IanSB/RGBtoHDMI/vhdl_RGB_12bit/RGBtoHDMI.vhdl

----------------------------------------------------------------------------------
-- Engineer:            David Banks & Ian Bradbury
--
-- Create Date:         15/7/2018
-- Module Name:         vhdl_RGB_12bit CPLD
-- Project Name:        vhdl_RGB_12bit
-- Target Devices:      XC9572XL
--
-- Version:             1.0
--
----------------------------------------------------------------------------------
library ieee;
use ieee.std_logic_1164.all;
use ieee.numeric_std.all;

entity vhdl_RGB_12bit is
    Port (
        -- From RGB Connector
        R3_I:      in    std_logic;
        G3_I:      in    std_logic;
        B3_I:      in    std_logic;
        R2_I:      in    std_logic;
        G2_I:      in    std_logic;
        B2_I:      in    std_logic;
        R1_I:      in    std_logic;
        G1_I:      in    std_logic;
        B1_I:      in    std_logic;
        R0_I:      in    std_logic;
        G0_I:      in    std_logic;
        B0_I:      in    std_logic;

        csync_I:   in    std_logic;
        vsync_I:   in    std_logic;

        analog:    inout std_logic;

        -- From Pi
        clk:       in    std_logic;
        sp_clken:  in    std_logic;

        -- To PI GPIO
        quad:      inout std_logic_vector(11 downto 0);
        psync:     out   std_logic;
        csync:     out   std_logic;

        -- User interface
        version:   in    std_logic
    );
end vhdl_RGB_12bit;

architecture Behavorial of vhdl_RGB_12bit is

    -- Version number: Design_Major_Minor
    -- Design: 0 = BBC CPLD
    --         1 = Alternative CPLD
    --         2 = Atom CPLD
    --         3 = six bit CPLD (if required);
    --         4 = RGB CPLD (TTL)
    --         C = RGB CPLD (Analog)

    constant VERSION_NUM_RGB_TTL    : std_logic_vector(11 downto 0) := x"495";
    constant VERSION_NUM_RGB_ANALOG : std_logic_vector(11 downto 0) := x"C95";

    -- The sampling counter serves several purposes:
    -- 1. Counts the delay the rising edge of nCSYNC and the first pixel
    -- 2. Counts within each pixel (bits 0, 1, 2, 3)
    -- 3. Counts multiple pixels if less than 9/12 bpp
    -- 4. Handles double buffering of alternative quad pixels (bit 5)
    --
    -- At the moment we don't count pixels with the line, the Pi does that

    signal counter  : unsigned(8 downto 0);

    -- synchronisation signals
    signal csync_counter : unsigned(1 downto 0);
    signal csync1        : std_logic;
    signal csync2        : std_logic;
    signal last          : std_logic;
    signal mux_sync      : std_logic;
    signal clamp_pulse   : std_logic;
    signal clamp_enable  : std_logic;
    signal latched_vsync : std_logic;
    signal edge_detected : std_logic;

    -- RGB Input Mux
    signal R3       :std_logic;
    signal G3       :std_logic;
    signal B3       :std_logic;
    signal R2       :std_logic;
    signal G2       :std_logic;
    signal B2       :std_logic;

     -- Sampling points
    constant INIT_SAMPLING_POINTS : std_logic_vector(15 downto 0) := "0000000000000000";
    signal sp_reg   : std_logic_vector(15 downto 0) := INIT_SAMPLING_POINTS;

    -- Break out of sp_reg
    signal offset     : std_logic_vector(3 downto 0);
    signal delay      : unsigned(1 downto 0);
    signal edge       : std_logic;
    signal rate       : std_logic_vector(1 downto 0);
    signal rateswitch : std_logic;
    signal invert     : std_logic;
    signal divider    : unsigned(1 downto 0);
    signal divdel2    : std_logic;
    signal mux        : std_logic;
	 signal clamp_on   : std_logic;    
	 
	 -- optional top bits of divider and delay	 
    signal divider2   : std_logic;
    signal delay2     : unsigned(1 downto 0);

	 
	 
    -- Shift registers for pixel samples

    signal shift_R  : std_logic_vector(3 downto 0);
    signal shift_G  : std_logic_vector(3 downto 0);
    signal shift_B  : std_logic_vector(3 downto 0);

    -- Sample pixel on next clock; pipelined to reduce the number of product terms

    signal sampleR   : std_logic;
    signal sampleG   : std_logic;
    signal sampleB   : std_logic;

    -- New sample available, toggle psync on next cycle

    signal toggle          : std_logic;

    -- rate = 00 is 3 bit capture with clamp_on 0/1 = clamp off/on (rateswitch used to add delay to leading edge)
    -- rate = 01 and rateswitch = '0' is 6 bit capture with clamp_on 0/1 = clamp off/on
    -- rate = 01 and rateswitch = '1' is 6 bit capture with 3 bit to 4 level encoding (clamp not usable in 4 level mode)
    -- rate = 10 and rateswitch = '0' is 1 bit capture on G3 with clamp_on 0/1 = clamp off/on, divdel2 used as extra delay bit
    -- rate = 10 and rateswitch = '1' is 1 bit capture on vsync with clamp_on 0/1 = clamp off/on, divdel2 used as extra delay bit
    -- rate = 11 and rateswitch = '0' and clamp_on = 0 is 9 bit capture using vsync_I as replacement G1 bit (will work on 8 bit board)
    -- rate = 11 and rateswitch = '0' and clamp_on = 1 is 12 bit capture
    -- rate = 11 and rateswitch = '1' is 9 bit capture with blanking on B3_I

begin
    offset     <= sp_reg(3 downto 0);
    delay      <= unsigned(sp_reg(5 downto 4));
    edge       <= sp_reg(6);
    rate       <= sp_reg(8 downto 7);
    rateswitch <= sp_reg(9);
    invert     <= sp_reg(10);
    divider    <= unsigned(sp_reg(12 downto 11));
    divdel2    <= sp_reg(13);
    mux        <= sp_reg(14);
clamp_on        <= sp_reg(15);
    mux_sync <= vsync_I when mux = '1' and version = '1' else csync_I;

    delay2 <= '0' & divdel2 when rate = "10" else "10";   --require 3 bits of delay plus leading zero in 1bpp mode

    G3 <= G2_I when vsync_I = '1' else G3_I;
    G2 <= G3_I when vsync_I = '1' else G2_I;

    B3 <= B2_I when B1_I = '1' else B3_I;
    B2 <= B3_I when B1_I = '1' else B2_I;

    R3 <= R2_I when R1_I = '1' else R3_I;
    R2 <= R3_I when R1_I = '1' else R2_I;

    process(clk)
    begin
        if rising_edge(clk) then
            -- synchronize CSYNC to the sampling clock
            csync1 <= mux_sync xor invert;

            -- De-glitch CSYNC
            --    csync1 is the possibly glitchy input
            --    csync2 is the filtered output
            if csync1 = csync2 then
                -- output same as input, reset the counter
                csync_counter <= to_unsigned(0, csync_counter'length);
            else
                -- output different to input
                csync_counter <= csync_counter + 1;
                -- if the difference lasts for N-1 cycles, update the output
                --if rate = "00" and edge = '1' and rateswitch = '1' then
                --    if csync_counter = 255 then
                --        csync2 <= csync1;
                --    end if;
                --else
                    if csync_counter(1 downto 0) = 3 then
                        csync2 <= csync1;
                    end if;
                --end if;
            end if;

            last <= csync2;

            if rate = "10" then
                divider2 <= '0';
            else
                divider2 <= divdel2;
            end if;

            -- pipeline leading and trailing edge detection
            if (edge = '0' and last = '0' and csync2 = '1') or (edge = '1' and last = '1' and csync2 = '0') then
                edge_detected <= '1';
            else
                edge_detected <= '0';
            end if;

            -- Counter is used to find sampling point for first pixel
            -- reset counter on the rising edge of csync
            if edge_detected = '1' then
                counter(8 downto 0) <= '1' & delay2 & delay & "0000";
                latched_vsync <= '0';           
            else
                if counter(3 downto 0) = unsigned(offset) then
                    if rate = "10" then
                        sampleR <= not(counter(4));
                        sampleB <= counter(4);
                    else
                        sampleR <= '1';
                        sampleB <= '1';
                    end if;
                    sampleG <= '1';
                else
                    sampleR <= '0';
                    sampleB <= '0';
                    sampleG <= '0';
                end if;
                if (divider2 & divider) = "000" then
                    if counter(3 downto 0) /= 2 then
                        if counter(counter'left) = '1' then
                            counter <= counter + 1;
                        else
                            counter(counter'left - 1 downto 0) <= counter(counter'left - 1 downto 0) + 1;
                        end if;
                    else
                        if counter(counter'left) = '1' then
                            counter <= counter + 14;
                        else
                            counter(counter'left - 1 downto 0) <= counter(counter'left - 1 downto 0) + 14;
                        end if;
                    end if;
                elsif counter(3 downto 0) /= (divider2 & divider & '1') then
                    if counter(counter'left) = '1' then
                        counter <= counter + 1;
                    else
                        counter(counter'left - 1 downto 0) <= counter(counter'left - 1 downto 0) + 1;
                    end if;
                elsif counter(counter'left) = '1' then
                    counter <= counter + (not(divider2 & divider) & '1');
                else
                    counter(counter'left - 1 downto 0) <= counter(counter'left - 1 downto 0) + (not(divider2 & divider) & '1');
                end if;
            end if;


            -- R Sample/shift register
            if sampleR = '1' then
                if rate = "11" and rateswitch = '0' and clamp_on = '1' then
                    shift_R <= R1_I & G2_I & B3_I & B0_I;             -- 12 bpp
                elsif rate = "11" and rateswitch = '0' and clamp_on = '0'  then
                    shift_R <= R1_I & G2_I & B3_I & B3_I;             -- 9 bpp
                elsif rate = "11" and rateswitch = '1' then
                    shift_R <= (R1_I and B3_I) & (G2_I and B3_I) & B3_I & (B0_I and B3_I);  -- 9 bpp lo blanked
                elsif rate = "10" and rateswitch = '0' then
                    shift_R <= G3_I & shift_R(3 downto 1);            -- 1 bpp on G3
                elsif rate = "10" and rateswitch = '1' then
                    shift_R <= vsync_I & shift_R(3 downto 1);         -- 1 bpp on Vsync
                elsif rate = "01" and rateswitch = '1' then
                    shift_R <= R2 & R3 & shift_R(3 downto 2);         -- 6 bpp 4 level
                elsif rate = "01" and rateswitch = '0' then
                    shift_R <= R2_I & R3_I & shift_R(3 downto 2);     -- 6 bpp
                else
                    shift_R <= R3_I & shift_R(3 downto 1);            -- 3 bpp
                end if;
            end if;

            -- G Sample/shift register
            if sampleG = '1' then
                if latched_vsync = '0' then
                    latched_vsync <= vsync_I;
                end if;
                if rate = "11" and rateswitch = '0' and clamp_on = '1' then
                    shift_G <= R2_I & G3_I & G0_I & B1_I;             -- 12 bpp
                elsif rate = "11" and rateswitch = '0' and clamp_on = '0' then
                    shift_G <= R2_I & G3_I & G3_I & B1_I;             -- 9 bpp
                elsif rate = "11" and rateswitch = '1' then
                    shift_G <= (R2_I and B3_I) & G3_I & (G0_I and B3_I) & (B1_I and B3_I);  -- 9 bpp lo blanked
                elsif rate = "01" and rateswitch = '1' then
                    shift_G <= G2 & G3 & shift_G(3 downto 2);         -- 6 bpp 4 level
                elsif rate = "01" and rateswitch = '0' then
                    shift_G <= G2_I & G3_I & shift_G(3 downto 2);     -- 6 bpp
                else
                    shift_G <= G3_I & shift_G(3 downto 1);            -- 3 bpp
                end if;
            end if;

            -- B Sample/shift register
             if sampleB = '1' then
                if rate = "11" and rateswitch = '0' and clamp_on = '1' then
                    shift_B <= R3_I & R0_I & G1_I & B2_I;             -- 12 bpp
                elsif rate = "11" and rateswitch = '0' and clamp_on = '0' then
                    shift_B <= R3_I & R3_I & vsync_I & B2_I;          -- 9 bpp with G1 on vsync_I
                elsif rate = "11" and rateswitch = '1' then
                    shift_B <= R3_I & (R0_I and B3_I) & (G1_I and B3_I) & (B2_I and B3_I);  -- 9 bpp lo blanked
                elsif rate = "10" and rateswitch = '0' then
                    shift_B <= G3_I & shift_B(3 downto 1);            -- 1 bpp on G3
                elsif rate = "10" and rateswitch = '1' then
                    shift_B <= vsync_I & shift_B(3 downto 1);         -- 1 bpp on Vsync
                elsif rate = "01" and rateswitch = '1' then
                    shift_B <= B2 & B3 & shift_B(3 downto 2);         -- 6 bpp 4 level
                elsif rate = "01" and rateswitch = '0' then
                    shift_B <= B2_I & B3_I & shift_B(3 downto 2);     -- 6 bpp
                else
                    shift_B <= B3_I & shift_B(3 downto 1);            -- 3 bpp
                end if;
            end if;

            -- Pipeline when to update the quad

            if ((rate = "00" and counter(5 downto 0) = 0) or      --  3 bpp
                (rate = "01" and counter(4 downto 0) = 0) or      --  6 bpp
                (rate = "10" and counter(6 downto 0) = 0) or      --  1 bpp
                (rate = "11" and counter(3 downto 0) = 0)) then   --  9 or 12 bpp
                toggle <= '1';  -- toggle is asserted in cycle 1
            else
                toggle <= '0';
            end if;
            if sp_clken = '0' then  
					-- Output quad register
					if version = '0' then
						 if analog = '1' then
							  quad <= VERSION_NUM_RGB_ANALOG;
						 else
							  quad <= VERSION_NUM_RGB_TTL;
						 end if;
					elsif toggle = '1' then
						 -- quad changes at the start of cycle 2
						 quad(11) <= shift_B(3);
						 quad(10) <= shift_G(3);
						 quad(9)  <= shift_R(3);
						 quad(8)  <= shift_B(2);
						 quad(7)  <= shift_G(2);
						 quad(6)  <= shift_R(2);
						 quad(5)  <= shift_B(1);
						 quad(4)  <= shift_G(1);
						 quad(3)  <= shift_R(1);
						 quad(2)  <= shift_B(0);
						 quad(1)  <= shift_G(0);
						 quad(0)  <= shift_R(0);
					end if;
				else
					if version = '1' then
					    if quad(8) = '0' then 
							  sp_reg(7 downto 0) <= quad(7 downto 0);	
                   else
						     sp_reg(15 downto 8) <= quad(7 downto 0);	
						 end if;					
					end if;
				end if;

            -- Output a skewed version of psync
            if version = '0' then
                psync <= vsync_I;
            elsif counter(counter'left) = '1' then
                psync <= '0';
            elsif counter(3 downto 0) = 2 then -- comparing with N gives N-1 cycles of skew
                if rate = "00" then
                    psync <= counter(6);       --  3 bpp: one edge for every 4 pixels
                elsif rate = "01" then
                    psync <= counter(5);       --  6 bpp: one edge for every 2 pixels
                elsif rate = "10" then
                    psync <= counter(7);       --  1 bpp: one edge for every 8 pixels
                elsif rate = "11" then
                    psync <= counter(4);       --  9/12 bpp: one edge for every pixel
                end if;
            end if;
        end if;
    end process;

    csync <= csync2 when version = '1' else latched_vsync; -- output the registered version to save a macro-cell

    -- csync2 is cleaned but delayed so OR with csync1 to remove delay on trailing edge of sync pulse
    -- clamp not usable in 4 LEVEL mode (rate = 10) or 8/12 bit mode (rate = 11) so use as multiplex signal instead
    clamp_pulse <= not(csync1 or csync2);
    clamp_enable <= '1' when mux = '1' else version;
    -- spdata is overloaded as clamp on/off
    analog <= 'Z' when clamp_enable = '0' else clamp_pulse and clamp_on;

end Behavorial;
