IanSB/RGBtoHDMI/src/osd.c

#include <stdio.h>
#include <stdlib.h>
#include <string.h>
#include <inttypes.h>
#include <ctype.h>
#include "defs.h"
#include "cpld.h"
#include "geometry.h"
#include "gitversion.h"
#include "info.h"
#include "logging.h"
#include "osd.h"
#include "rpi-gpio.h"
#include "rpi-mailbox.h"
#include "rpi-mailbox-interface.h"
#include "saa5050_font.h"
#include "8x8_font.h"
#include "rgb_to_fb.h"
#include "rgb_to_hdmi.h"
#include "filesystem.h"
#include "fatfs/ff.h"
#include "jtag/update_cpld.h"

// =============================================================
// Definitions for the size of the OSD
// =============================================================

#define NLINES         30

#define FONT_THRESHOLD    25

#define LINELEN        42

#define MAX_MENU_DEPTH  4

#define DEFAULT_CPLD_FIRMWARE_DIR "/cpld_firmware/recovery"

// =============================================================
// Definitions for the key press interface
// =============================================================

#define LONG_KEY_PRESS_DURATION 25

// =============================================================
// Main states that the OSD can be in
// =============================================================

typedef enum {
   IDLE,          // Wait for button to be pressed
   DURATION,      // Determine whether short or long button press

   MIN_ACTION,    // Marker state, never actually used

   // The next N states are the pre-defined action states
   // At most 6 of these can be bound to button presses (3 buttons, long/short)
   A0_LAUNCH,     // Action 0: Launch menu system
   A1_CAPTURE,    // Action 1: Screen capture
   A2_CLOCK_CAL,  // Action 2: HDMI clock calibration
   A3_AUTO_CAL,   // Action 3: Auto calibration
   A4_SCANLINES,  // Action 4: Toggle scanlines
   A5_SPARE,      // Action 5: Spare
   A6_SPARE,      // Action 6: Spare
   A7_SPARE,      // Action 7: Spare

   MAX_ACTION,    // Marker state, never actually used

   CLOCK_CAL0,    // Intermediate state in clock calibration
   CLOCK_CAL1,    // Intermediate state in clock calibration
   MENU,          // Browsing a menu
   PARAM,         // Changing the value of a menu item
   INFO           // Viewing an info panel
} osd_state_t;

// =============================================================
// Friently names for certain OSD feature values
// =============================================================


static char *default_palette_names[] = {
   "RGB",
   "RGBI",
   "RGBI_(CGA)",
   "RGBI_(Spectrum)",
   "RGBrgb_(Spectrum)",
   "RGBrgb_(Amstrad)",
   "RrGgBb_(EGA)",
   "MDA-Hercules",
   "Dragon-CoCo",
   "Dragon-CoCo_Full",
   "Dragon-CoCo_Emu",
   "Atom_MKII",
   "Atom_MKII_Plus",
   "Atom_MKII_Full",
   "Mono_(2_level)",
   "Mono_(3_level)",
   "Mono_(4_level)",
   "Mono_(6_level)",
 //  "TI-99-4a_14Col",
   "Spectrum_48K_9Col",
   "Colour_Genie_S24",
   "Colour_Genie_S25",
   "Colour_Genie_N25"
};

static const char *palette_control_names[] = {
   "Off",
   "In Band Commands",
   "NTSC Artifacting"
};

static const char *return_names[] = {
   "Start",
   "End"
};

static const char *vlockmode_names[] = {
   "Genlocked (Exact)",
   "1000ppm Fast",
   "2000ppm Fast",
   "Unlocked",
   "2000ppm Slow",
   "1000ppm Slow"
};

static const char *deinterlace_names[] = {
   "None",
   "Simple Bob",
   "Simple Motion 1",
   "Simple Motion 2",
   "Simple Motion 3",
   "Simple Motion 4",
   "Advanced Motion"
};

#ifdef MULTI_BUFFER
static const char *nbuffer_names[] = {
   "Single buffered",
   "Double buffered",
   "Triple buffered",
   "Quadruple buffered"
};
#endif

static const char *autoswitch_names[] = {
   "Off",
   "Sub-Profile",
   "BBC Mode 7"
};

static const char *overscan_names[] = {
   "Auto",
   "Maximum",
   "Halfway",
   "Minimum"
};

static const char *colour_names[] = {
   "Normal",
   "Monochrome",
   "Green",
   "Amber"
};

static const char *invert_names[] = {
   "Normal",
   "Invert RGB/YUV",
   "Invert G/Y"
};

static const char *scaling_names[] = {
   "Integer / Sharp",
   "Integer / Soft",
   "Integer / Very Soft",
   "Fill 4:3 / Soft",
   "Fill 4:3 / Very Soft",
   "Fill All / Soft",
   "Fill All / Very Soft"
};

static const char *frontend_names[] = {
   "3 BIT RGB",
   "Atom",
   "6 BIT RGB",
   "6 BIT RGB Analog Issue 3",
   "6 BIT RGB Analog Issue 2",   
   "6 BIT RGB Analog Issue 1A",
   "6 BIT RGB Analog Issue 1B",
   "6 BIT YUV Analog Issue 3",
   "6 BIT YUV Analog Issue 2"   
};

static const char *vlockspeed_names[] = {
   "Slow (333PPM)",
   "Medium (1000PPM)",
   "Fast (2000PPM)"
};

static const char *vlockadj_names[] = {
   "-5% to +5%",
   "Full Range",
   "Up to 260Mhz"
};

static const char *fontsize_names[] = {
   "Always 8x8",
   "Auto 12x20 4bpp",
   "Auto 12x20 8bpp"
};

static const char *even_scaling_names[] = {
   "Even",
   "Uneven (3:2>>4:3)"
};

// =============================================================
// Feature definitions
// =============================================================

enum {
   F_AUTOSWITCH,
   F_RESOLUTION,
   F_SCALING,
   F_FRONTEND,
   F_PROFILE,
   F_SUBPROFILE,
   F_PALETTE,
   F_PALETTECONTROL,
   F_DEINTERLACE,
   F_M7SCALING,
   F_NORMALSCALING,
   F_COLOUR,
   F_INVERT,
   F_SCANLINES,
   F_SCANLINESINT,
   F_OVERSCAN,
   F_CAPSCALE,
   F_FONTSIZE,
   F_BORDER,
   F_VSYNC,
   F_VLOCKMODE,
   F_VLOCKLINE,
   F_VLOCKSPEED,
   F_VLOCKADJ,
#ifdef MULTI_BUFFER
   F_NBUFFERS,
#endif
   F_RETURN,
   F_DEBUG
};

static param_t features[] = {
   {      F_AUTOSWITCH,       "Auto Switch",       "auto_switch", 0, NUM_AUTOSWITCHES - 1, 1 },
   {      F_RESOLUTION,        "Resolution",        "resolution", 0,                    0, 1 },
   {         F_SCALING,           "Scaling",           "scaling", 0,      NUM_SCALING - 1, 1 },
   {        F_FRONTEND,         "Interface",         "interface", 0,    NUM_FRONTENDS - 1, 1 },
   {         F_PROFILE,           "Profile",           "profile", 0,                    0, 1 },
   {      F_SUBPROFILE,       "Sub-Profile",        "subprofile", 0,                    0, 1 },
   {         F_PALETTE,           "Palette",           "palette", 0,                    0, 1 },
   {  F_PALETTECONTROL,   "Palette Control",   "palette_control", 0,     NUM_CONTROLS - 1, 1 },
   {     F_DEINTERLACE,"Teletext Deinterlace", "teletext_deinterlace", 0, NUM_DEINTERLACES - 1, 1 },
   {       F_M7SCALING,  "Teletext Scaling",     "teletext_scaling", 0,   NUM_ESCALINGS - 1, 1 },
   {   F_NORMALSCALING,"Progressive Scaling",    "progressive_scaling", 0, NUM_ESCALINGS - 1, 1 },
   {          F_COLOUR,     "Output Colour",     "output_colour", 0,      NUM_COLOURS - 1, 1 },
   {          F_INVERT,     "Output Invert",     "output_invert", 0,       NUM_INVERT - 1, 1 },
   {       F_SCANLINES,         "Scanlines",         "scanlines", 0,                    1, 1 },
   {    F_SCANLINESINT,    "Scanline Level",    "scanline_level", 0,                   15, 1 },
   {        F_OVERSCAN,          "Overscan",          "overscan", 0,     NUM_OVERSCAN - 1, 1 },
   {        F_CAPSCALE, "ScreenCap Scaling", "screencap_scaling", 0,                    1, 1 },
   {        F_FONTSIZE,         "Font Size",         "font_size", 0,     NUM_FONTSIZE - 1, 1 },
   {          F_BORDER,     "Border Colour",     "border_colour", 0,                  255, 1 },
   {           F_VSYNC,  "V Sync Indicator",   "vsync_indicator", 0,                    1, 1 },
   {       F_VLOCKMODE,       "V Lock Mode",        "vlock_mode", 0,         NUM_HDMI - 1, 1 },
   {       F_VLOCKLINE,      "Genlock Line",      "genlock_line",35,                  140, 1 },
   {      F_VLOCKSPEED,     "Genlock Speed",     "genlock_speed", 0,   NUM_VLOCKSPEED - 1, 1 },
   {        F_VLOCKADJ,    "Genlock Adjust",    "genlock_adjust", 0,     NUM_VLOCKADJ - 2, 1 },  //-2 so disables 260 mhz for now
#ifdef MULTI_BUFFER
   {        F_NBUFFERS,       "Num Buffers",       "num_buffers", 0,                    3, 1 },
#endif
   {          F_RETURN,   "Return Position",            "return", 0,                    1, 1 },
   {           F_DEBUG,             "Debug",             "debug", 0,                    1, 1 },
   {                -1,                NULL,                NULL, 0,                    0, 0 }
};

// =============================================================
// Menu definitions
// =============================================================


typedef enum {
   I_MENU,     // Item points to a sub-menu
   I_FEATURE,  // Item is a "feature" (i.e. managed by the osd)
   I_GEOMETRY, // Item is a "geometry" (i.e. managed by the geometry)
   I_PARAM,    // Item is a "parameter" (i.e. managed by the cpld)
   I_INFO,     // Item is an info screen
   I_BACK,     // Item is a link back to the previous menu
   I_SAVE,     // Item is a saving profile option
   I_RESTORE,  // Item is a restoring a profile option
   I_UPDATE,   // Item is a cpld update
   I_CALIBRATE // Item is a calibration update
} item_type_t;

typedef struct {
   item_type_t       type;
} base_menu_item_t;

typedef struct menu {
   char *name;
   void            (*rebuild)(struct menu *this);
   base_menu_item_t *items[];
} menu_t;

typedef struct {
   item_type_t       type;
   menu_t           *child;
} child_menu_item_t;

typedef struct {
   item_type_t       type;
   param_t          *param;
} param_menu_item_t;

typedef struct {
   item_type_t       type;
   char             *name;
   void            (*show_info)(int line);
} info_menu_item_t;

typedef struct {
   item_type_t       type;
   char             *name;
} back_menu_item_t;

typedef struct {
   item_type_t       type;
   char             *name;
} action_menu_item_t;

static void info_source_summary(int line);
static void info_system_summary(int line);
static void info_cal_summary(int line);
static void info_cal_detail(int line);
static void info_cal_raw(int line);
static void info_credits(int line);
static void info_reboot(int line);

static void rebuild_geometry_menu(menu_t *menu);
static void rebuild_sampling_menu(menu_t *menu);
static void rebuild_update_cpld_menu(menu_t *menu);

static info_menu_item_t source_summary_ref   = { I_INFO, "Source Summary",      info_source_summary};
static info_menu_item_t system_summary_ref   = { I_INFO, "System Summary",      info_system_summary};
static info_menu_item_t cal_summary_ref      = { I_INFO, "Calibration Summary", info_cal_summary};
static info_menu_item_t cal_detail_ref       = { I_INFO, "Calibration Detail",  info_cal_detail};
static info_menu_item_t cal_raw_ref          = { I_INFO, "Calibration Raw",     info_cal_raw};
static info_menu_item_t credits_ref          = { I_INFO, "Credits",             info_credits};
static info_menu_item_t reboot_ref           = { I_INFO, "Reboot",              info_reboot};

static back_menu_item_t back_ref             = { I_BACK, "Return"};
static action_menu_item_t save_ref           = { I_SAVE, "Save Configuration"};
static action_menu_item_t restore_ref        = { I_RESTORE, "Restore Default Configuration"};
static action_menu_item_t cal_sampling_ref   = { I_CALIBRATE, "Auto Calibrate Video Sampling"};


static menu_t update_cpld_menu = {
   "Update CPLD Menu",
   rebuild_update_cpld_menu,
   {
      // Allow space for max 30 params
      NULL,
      NULL,
      NULL,
      NULL,
      NULL,
      NULL,
      NULL,
      NULL,
      NULL,
      NULL,
      NULL,
      NULL,
      NULL,
      NULL,
      NULL,
      NULL,
      NULL,
      NULL,
      NULL,
      NULL,
      NULL,
      NULL,
      NULL,
      NULL,
      NULL,
      NULL,
      NULL,
      NULL,
      NULL,
      NULL,
      NULL
   }
};

static child_menu_item_t update_cpld_menu_ref = { I_MENU, &update_cpld_menu};

static menu_t info_menu = {
   "Info Menu",
   NULL,
   {
      (base_menu_item_t *) &back_ref,
      (base_menu_item_t *) &source_summary_ref,
      (base_menu_item_t *) &system_summary_ref,
      (base_menu_item_t *) &cal_summary_ref,
      (base_menu_item_t *) &cal_detail_ref,
      (base_menu_item_t *) &cal_raw_ref,
      (base_menu_item_t *) &credits_ref,
      (base_menu_item_t *) &reboot_ref,
      (base_menu_item_t *) &update_cpld_menu_ref,
      NULL
   }
};

static param_menu_item_t profile_ref         = { I_FEATURE, &features[F_PROFILE]        };
static param_menu_item_t subprofile_ref      = { I_FEATURE, &features[F_SUBPROFILE]     };
static param_menu_item_t resolution_ref      = { I_FEATURE, &features[F_RESOLUTION]     };
static param_menu_item_t scaling_ref         = { I_FEATURE, &features[F_SCALING]        };
static param_menu_item_t frontend_ref        = { I_FEATURE, &features[F_FRONTEND]       };
static param_menu_item_t overscan_ref        = { I_FEATURE, &features[F_OVERSCAN]       };
static param_menu_item_t capscale_ref        = { I_FEATURE, &features[F_CAPSCALE]       };
static param_menu_item_t border_ref          = { I_FEATURE, &features[F_BORDER]         };
static param_menu_item_t palettecontrol_ref  = { I_FEATURE, &features[F_PALETTECONTROL] };
static param_menu_item_t palette_ref         = { I_FEATURE, &features[F_PALETTE]        };
static param_menu_item_t deinterlace_ref     = { I_FEATURE, &features[F_DEINTERLACE]    };
static param_menu_item_t m7scaling_ref       = { I_FEATURE, &features[F_M7SCALING]      };
static param_menu_item_t normalscaling_ref   = { I_FEATURE, &features[F_NORMALSCALING]  };
static param_menu_item_t scanlines_ref       = { I_FEATURE, &features[F_SCANLINES]      };
static param_menu_item_t scanlinesint_ref    = { I_FEATURE, &features[F_SCANLINESINT]   };
static param_menu_item_t colour_ref          = { I_FEATURE, &features[F_COLOUR]         };
static param_menu_item_t invert_ref          = { I_FEATURE, &features[F_INVERT]         };
static param_menu_item_t fontsize_ref        = { I_FEATURE, &features[F_FONTSIZE]       };
static param_menu_item_t vsync_ref           = { I_FEATURE, &features[F_VSYNC]          };
static param_menu_item_t vlockmode_ref       = { I_FEATURE, &features[F_VLOCKMODE]      };
static param_menu_item_t vlockline_ref       = { I_FEATURE, &features[F_VLOCKLINE]      };
static param_menu_item_t vlockspeed_ref      = { I_FEATURE, &features[F_VLOCKSPEED]     };
static param_menu_item_t vlockadj_ref        = { I_FEATURE, &features[F_VLOCKADJ]       };
#ifdef MULTI_BUFFER
static param_menu_item_t nbuffers_ref        = { I_FEATURE, &features[F_NBUFFERS]       };
#endif
static param_menu_item_t autoswitch_ref      = { I_FEATURE, &features[F_AUTOSWITCH]     };
static param_menu_item_t return_ref          = { I_FEATURE, &features[F_RETURN]         };
static param_menu_item_t debug_ref           = { I_FEATURE, &features[F_DEBUG]          };

static menu_t preferences_menu = {
   "Preferences Menu",
   NULL,
   {
      (base_menu_item_t *) &back_ref,
      (base_menu_item_t *) &palette_ref,
      (base_menu_item_t *) &colour_ref,
      (base_menu_item_t *) &invert_ref,
      (base_menu_item_t *) &border_ref,
      (base_menu_item_t *) &palettecontrol_ref,
      (base_menu_item_t *) &scanlines_ref,
      (base_menu_item_t *) &scanlinesint_ref,
      (base_menu_item_t *) &deinterlace_ref,
      (base_menu_item_t *) &m7scaling_ref,
      (base_menu_item_t *) &normalscaling_ref,
      (base_menu_item_t *) &overscan_ref,
      (base_menu_item_t *) &capscale_ref,
      NULL
   }
};

static menu_t settings_menu = {
   "Settings Menu",
   NULL,
   {
      (base_menu_item_t *) &back_ref,
      (base_menu_item_t *) &fontsize_ref,
      (base_menu_item_t *) &vsync_ref,
      (base_menu_item_t *) &vlockmode_ref,
      (base_menu_item_t *) &vlockline_ref,
      (base_menu_item_t *) &vlockspeed_ref,
      (base_menu_item_t *) &vlockadj_ref,
      (base_menu_item_t *) &nbuffers_ref,
      (base_menu_item_t *) &return_ref,
      (base_menu_item_t *) &debug_ref,
      NULL
   }
};

static param_menu_item_t dynamic_item[] = {
   { I_PARAM, NULL },
   { I_PARAM, NULL },
   { I_PARAM, NULL },
   { I_PARAM, NULL },
   { I_PARAM, NULL },
   { I_PARAM, NULL },
   { I_PARAM, NULL },
   { I_PARAM, NULL },
   { I_PARAM, NULL },
   { I_PARAM, NULL },
   { I_PARAM, NULL },
   { I_PARAM, NULL },
   { I_PARAM, NULL },
   { I_PARAM, NULL },
   { I_PARAM, NULL },
   { I_PARAM, NULL },
   { I_PARAM, NULL },
   { I_PARAM, NULL },
   { I_PARAM, NULL },
   { I_PARAM, NULL },
   { I_PARAM, NULL },
   { I_PARAM, NULL },
   { I_PARAM, NULL },
   { I_PARAM, NULL },
   { I_PARAM, NULL },
   { I_PARAM, NULL },
   { I_PARAM, NULL },
   { I_PARAM, NULL },
   { I_PARAM, NULL },
   { I_PARAM, NULL }
};

static menu_t geometry_menu = {
   "Geometry Menu",
   rebuild_geometry_menu,
   {
      // Allow space for max 30 params
      NULL,
      NULL,
      NULL,
      NULL,
      NULL,
      NULL,
      NULL,
      NULL,
      NULL,
      NULL,
      NULL,
      NULL,
      NULL,
      NULL,
      NULL,
      NULL,
      NULL,
      NULL,
      NULL,
      NULL,
      NULL,
      NULL,
      NULL,
      NULL,
      NULL,
      NULL,
      NULL,
      NULL,
      NULL,
      NULL,
      NULL
   }
};

static menu_t sampling_menu = {
   "Sampling Menu",
   rebuild_sampling_menu,
   {
      // Allow space for max 30 params
      NULL,
      NULL,
      NULL,
      NULL,
      NULL,
      NULL,
      NULL,
      NULL,
      NULL,
      NULL,
      NULL,
      NULL,
      NULL,
      NULL,
      NULL,
      NULL,
      NULL,
      NULL,
      NULL,
      NULL,
      NULL,
      NULL,
      NULL,
      NULL,
      NULL,
      NULL,
      NULL,
      NULL,
      NULL,
      NULL,
      NULL
   }
};

static child_menu_item_t info_menu_ref        = { I_MENU, &info_menu        };
static child_menu_item_t preferences_menu_ref = { I_MENU, &preferences_menu };
static child_menu_item_t settings_menu_ref    = { I_MENU, &settings_menu    };
static child_menu_item_t geometry_menu_ref    = { I_MENU, &geometry_menu    };
static child_menu_item_t sampling_menu_ref    = { I_MENU, &sampling_menu    };

static menu_t main_menu = {
   "Main Menu",
   NULL,
   {
      (base_menu_item_t *) &back_ref,
      (base_menu_item_t *) &info_menu_ref,
      (base_menu_item_t *) &preferences_menu_ref,
      (base_menu_item_t *) &settings_menu_ref,
      (base_menu_item_t *) &geometry_menu_ref,
      (base_menu_item_t *) &sampling_menu_ref,
      (base_menu_item_t *) &save_ref,
      (base_menu_item_t *) &restore_ref,
      (base_menu_item_t *) &cal_sampling_ref,
      (base_menu_item_t *) &resolution_ref,
      (base_menu_item_t *) &scaling_ref,
      (base_menu_item_t *) &frontend_ref,
      (base_menu_item_t *) &profile_ref,
      (base_menu_item_t *) &autoswitch_ref,
      (base_menu_item_t *) &subprofile_ref,
      NULL
   }
};

// =============================================================
// Static local variables
// =============================================================

static char buffer[LINELEN * NLINES];

static int attributes[NLINES];

// Mapping table for expanding 12-bit row to 24 bit pixel (3 words) with 4 bits/pixel
static uint32_t double_size_map_4bpp[0x1000 * 3];

// Mapping table for expanding 12-bit row to 12 bit pixel (2 words + 2 words) with 4 bits/pixel
static uint32_t normal_size_map_4bpp[0x1000 * 4];

// Mapping table for expanding 12-bit row to 24 bit pixel (6 words) with 8 bits/pixel
static uint32_t double_size_map_8bpp[0x1000 * 6];

// Mapping table for expanding 12-bit row to 12 bit pixel (3 words) with 8 bits/pixel
static uint32_t normal_size_map_8bpp[0x1000 * 3];

// Mapping table for expanding 8-bit row to 16 bit pixel (2 words) with 4 bits/pixel
static uint32_t double_size_map8_4bpp[0x1000 * 2];

// Mapping table for expanding 8-bit row to 8 bit pixel (1 word) with 4 bits/pixel
static uint32_t normal_size_map8_4bpp[0x1000 * 1];

// Mapping table for expanding 8-bit row to 16 bit pixel (4 words) with 8 bits/pixel
static uint32_t double_size_map8_8bpp[0x1000 * 4];

// Mapping table for expanding 8-bit row to 8 bit pixel (2 words) with 8 bits/pixel
static uint32_t normal_size_map8_8bpp[0x1000 * 2];

// Temporary buffer for assembling OSD lines
static char message[80];

// Temporary filename for assembling OSD lines
static char filename[80];

// Is the OSD currently active
static int active = 0;

// Main state of the OSD
osd_state_t osd_state = IDLE;

// Current menu depth
static int depth = 0;

// Currently active menu
static menu_t *current_menu[MAX_MENU_DEPTH];

// Index to the currently selected menu
static int current_item[MAX_MENU_DEPTH];

// Currently selected palette setting
static int palette   = PALETTE_RGB;

//osd high water mark (highest line number used)
static int osd_hwm = 0;

static int all_frontends[16] = {0,0,0,0,0,0,0,0,0,0,0,0,0,0,0,0};

// Default action map, maps from physical key press to action
static osd_state_t action_map[] = {
   A0_LAUNCH,    //   0 - SW1 short press
   A1_CAPTURE,   //   1 - SW2 short press
   A2_CLOCK_CAL, //   2 - SW3 short press
   A4_SCANLINES, //   3 - SW1 long press
   A5_SPARE,     //   4 - SW2 long press
   A3_AUTO_CAL,  //   5 - SW3 long press
};

#define NUM_ACTIONS (sizeof(action_map) / sizeof(osd_state_t))

// Default keymap, used for menu navigation
static int key_enter     = OSD_SW1;
static int key_menu_up   = OSD_SW3;
static int key_menu_down = OSD_SW2;
static int key_value_dec = OSD_SW2;
static int key_value_inc = OSD_SW3;



// Whether the menu back pointer is at the start (0) or end (1) of the menu
static int return_at_end = 0;
static char config_buffer[MAX_CONFIG_BUFFER_SIZE];
static char save_buffer[MAX_BUFFER_SIZE];
static char default_buffer[MAX_BUFFER_SIZE];
static char main_buffer[MAX_BUFFER_SIZE];
static char sub_default_buffer[MAX_BUFFER_SIZE];
static char sub_profile_buffers[MAX_SUB_PROFILES][MAX_BUFFER_SIZE];
static int has_sub_profiles[MAX_PROFILES];
static char profile_names[MAX_PROFILES][MAX_PROFILE_WIDTH];
static char sub_profile_names[MAX_SUB_PROFILES][MAX_PROFILE_WIDTH];
static char resolution_names[MAX_NAMES][MAX_NAMES_WIDTH];

static uint32_t palette_data[256];
static unsigned char equivalence[256];

static char palette_names[MAX_NAMES][MAX_NAMES_WIDTH];
static uint32_t palette_array[MAX_NAMES][256];

typedef struct {
   int clock;
   int line_len;
   int clock_ppm;
   int lines_per_frame;
   int sync_type;
   int lower_limit;
   int upper_limit;
} autoswitch_info_t;

static autoswitch_info_t autoswitch_info[MAX_SUB_PROFILES];

static char cpld_firmware_dir[256] = DEFAULT_CPLD_FIRMWARE_DIR;

// =============================================================
// Private Methods
// =============================================================

static void cycle_menu(menu_t *menu) {
   // count the number of items in the menu, excluding the back reference
   int nitems = 0;
   base_menu_item_t **mp = menu->items;
   while (*mp++) {
      nitems++;
   }
   nitems--;
   base_menu_item_t *first = *(menu->items);
   base_menu_item_t *last = *(menu->items + nitems);
   base_menu_item_t *back = (base_menu_item_t *)&back_ref;
   if (return_at_end) {
      if (first == back) {
         for (int i = 0; i < nitems; i++) {
            *(menu->items + i) = *(menu->items + i + 1);
         }
         *(menu->items + nitems) = back;
      }
   } else {
      if (last == back) {
         for (int i = nitems; i > 0; i--) {
            *(menu->items + i) = *(menu->items + i - 1);
         }
         *(menu->items) = back;
      }
   }
}

static void cycle_menus() {
   cycle_menu(&main_menu);
   cycle_menu(&info_menu);
   cycle_menu(&preferences_menu);
   cycle_menu(&settings_menu);
}

static int get_feature(int num) {
   switch (num) {
   case F_PROFILE:
      return get_profile();
   case F_SUBPROFILE:
      return get_subprofile();
   case F_RESOLUTION:
      return get_resolution();
   case F_SCALING:
      return get_scaling();
   case F_FRONTEND:
      return get_frontend();
   case F_OVERSCAN:
      return get_overscan();
   case F_CAPSCALE:
      return get_capscale();
   case F_BORDER:
      return get_border();
   case F_FONTSIZE:
      return get_fontsize();
   case F_DEINTERLACE:
      return get_deinterlace();
   case F_M7SCALING:
      return get_m7scaling();
   case F_NORMALSCALING:
      return get_normalscaling();
   case F_PALETTE:
      return palette;
   case F_PALETTECONTROL:
      return get_paletteControl();
   case F_SCANLINES:
      return get_scanlines();
   case F_SCANLINESINT:
      return get_scanlines_intensity();
   case F_COLOUR:
      return get_colour();
   case F_INVERT:
      return get_invert();
   case F_VSYNC:
      return get_vsync();
   case F_VLOCKMODE:
      return get_vlockmode();
   case F_VLOCKLINE:
      return get_vlockline();
   case F_VLOCKSPEED:
      return get_vlockspeed();
   case F_VLOCKADJ:
      return get_vlockadj();
#ifdef MULTI_BUFFER
   case F_NBUFFERS:
      return get_nbuffers();
#endif
   case F_AUTOSWITCH:
      return get_autoswitch();
   case F_RETURN:
      return return_at_end;
   case F_DEBUG:
      return get_debug();
   }
   return -1;
}

static void set_feature(int num, int value) {
   if (value < features[num].min) {
      value = features[num].min;
   }
   if (value > features[num].max) {
      value = features[num].max;
   }
   switch (num) {
   case F_PROFILE:
      set_profile(value);
      load_profiles(value, 1);
      process_profile(value);
      set_feature(F_SUBPROFILE, 0);
      break;
   case F_SUBPROFILE:
      set_subprofile(value);
      process_sub_profile(get_profile(), value);
      break;
   case F_RESOLUTION:
      set_resolution(value, resolution_names[value], 1);
      break;
   case F_SCALING:
      set_scaling(value, 1);
      break;
   case F_FRONTEND:
      set_frontend(value, 1);
      break;
   case F_DEINTERLACE:
      set_deinterlace(value);
      break;
   case F_M7SCALING:
      set_m7scaling(value);
      break;
   case F_NORMALSCALING:
      set_normalscaling(value);
      break;
   case F_OVERSCAN:
      set_overscan(value);
      break;
   case F_CAPSCALE:
      set_capscale(value);
      break;
   case F_BORDER:
      set_border(value);
      break;
   case F_FONTSIZE:
      if(active) {
         osd_clear();
         set_fontsize(value);
         osd_refresh();
      } else {
         set_fontsize(value);
      }
      break;
   case F_PALETTE:
      palette = value;
      osd_update_palette();
      break;
   case F_PALETTECONTROL:
      set_paletteControl(value);
      osd_update_palette();
      break;
   case F_SCANLINES:
      set_scanlines(value);
      break;
   case F_SCANLINESINT:
      set_scanlines_intensity(value);
      break;
   case F_COLOUR:
      set_colour(value);
      osd_update_palette();
      break;
   case F_INVERT:
      set_invert(value);
      osd_update_palette();
      break;
   case F_VSYNC:
      set_vsync(value);
      break;
   case F_VLOCKMODE:
      set_vlockmode(value);
      break;
   case F_VLOCKLINE:
      set_vlockline(value);
      break;
   case F_VLOCKSPEED:
      set_vlockspeed(value);
      break;
   case F_VLOCKADJ:
      set_vlockadj(value);
      break;
#ifdef MULTI_BUFFER
   case F_NBUFFERS:
      set_nbuffers(value);
      break;
#endif
   case F_RETURN:
      return_at_end = value;
      cycle_menus();
      break;
   case F_DEBUG:
      set_debug(value);
      osd_update_palette();
      break;
   case F_AUTOSWITCH:
      set_autoswitch(value);
      break;
   }
}

// Wrapper to extract the name of a menu item
static const char *item_name(base_menu_item_t *item) {
   switch (item->type) {
   case I_MENU:
      return ((child_menu_item_t *)item)->child->name;
   case I_FEATURE:
   case I_GEOMETRY:
   case I_UPDATE:
   case I_PARAM:
      return ((param_menu_item_t *)item)->param->label;
   case I_INFO:
      return ((info_menu_item_t *)item)->name;
   case I_BACK:
      return ((back_menu_item_t *)item)->name;
   default:
      // Otherwise, default to a single action menu item type
      return ((action_menu_item_t *)item)->name;
   }
}

// Test if a parameter is a simple boolean
static int is_boolean_param(param_menu_item_t *param_item) {
   return param_item->param->min == 0 && param_item->param->max == 1;
}

// Test if a paramater is toggleable (i.e. just two valid values)
static int is_toggleable_param(param_menu_item_t *param_item) {
   return param_item->param->min + param_item->param->step == param_item->param->max;
}

// Set wrapper to abstract different between I_FEATURE, I_GEOMETRY and I_PARAM
static void set_param(param_menu_item_t *param_item, int value) {
   item_type_t type = param_item->type;
   if (type == I_FEATURE) {
      set_feature(param_item->param->key, value);
   } else if (type == I_GEOMETRY) {
      geometry_set_value(param_item->param->key, value);
   } else {
      cpld->set_value(param_item->param->key, value);
   }
}

// Get wrapper to abstract different between I_FEATURE, I_GEOMETRY and I_PARAM
static int get_param(param_menu_item_t *param_item) {
   item_type_t type = param_item->type;
   if (type == I_FEATURE) {
      return get_feature(param_item->param->key);
   } else if (type == I_GEOMETRY) {
      return geometry_get_value(param_item->param->key);
   } else {
      return cpld->get_value(param_item->param->key);
   }
}

// Toggle a parameter that only has two legal values (it's min and max)
static void toggle_param(param_menu_item_t *param_item) {
   if (get_param(param_item) == param_item->param->max) {
      set_param(param_item, param_item->param->min);
   } else {
      set_param(param_item, param_item->param->max);
   }
}

static const char *get_param_string(param_menu_item_t *param_item) {
   static char number[16];
   item_type_t type = param_item->type;
   param_t   *param = param_item->param;
   // Read the current value of the specified feature
   int value = get_param(param_item);
   // Convert certain features to human readable strings
   if (type == I_FEATURE) {
      switch (param->key) {
      case F_PROFILE:
         return profile_names[value];
      case F_SUBPROFILE:
         return sub_profile_names[value];
      case F_RESOLUTION:
         return resolution_names[value];
      case F_SCALING:
         return scaling_names[value];
      case F_FRONTEND:
         return frontend_names[value];
      case F_OVERSCAN:
         return overscan_names[value];
      case F_COLOUR:
         return colour_names[value];
      case F_INVERT:
         return invert_names[value];
      case F_FONTSIZE:
         return fontsize_names[value];
      case F_PALETTE:
         return palette_names[value];
      case F_PALETTECONTROL:
         return palette_control_names[value];
      case F_AUTOSWITCH:
         return autoswitch_names[value];
      case F_DEINTERLACE:
         return deinterlace_names[value];
      case F_M7SCALING:
         return even_scaling_names[value];
      case F_NORMALSCALING:
         return even_scaling_names[value];
      case F_VLOCKMODE:
         return vlockmode_names[value];
      case F_VLOCKSPEED:
         return vlockspeed_names[value];
      case F_VLOCKADJ:
         return vlockadj_names[value];
#ifdef MULTI_BUFFER
      case F_NBUFFERS:
         return nbuffer_names[value];
#endif
      case F_RETURN:
         return return_names[value];
      }
   } else if (type == I_GEOMETRY) {
      const char *value_str = geometry_get_value_string(param->key);
      if (value_str) {
         return value_str;
      }
   } else {
      const char *value_str = cpld->get_value_string(param->key);
      if (value_str) {
         return value_str;
      }
   }
   if (is_boolean_param(param_item)) {
      return value ? "On" : "Off";
   }
   sprintf(number, "%d", value);
   return number;
}

static volatile uint32_t *gpioreg = (volatile uint32_t *)(PERIPHERAL_BASE + 0x101000UL);

static void info_system_summary(int line) {
   sprintf(message, "RGBtoHDMI Version: %s", GITVERSION);
   osd_set(line++, 0, message);
   sprintf(message, "     CPLD Version: %s v%x.%x",
           cpld->name,
           (cpld->get_version() >> VERSION_MAJOR_BIT) & 0xF,
           (cpld->get_version() >> VERSION_MINOR_BIT) & 0xF);
   osd_set(line++, 0, message);
   int ANA1_PREDIV = (gpioreg[PLLA_ANA1] >> 14) & 1;
   int NDIV = (gpioreg[PLLA_CTRL] & 0x3ff) << ANA1_PREDIV;
   int FRAC = gpioreg[PLLA_FRAC] << ANA1_PREDIV;
   int clockA = (double) (CRYSTAL * ((double)NDIV + ((double)FRAC) / ((double)(1 << 20))) + 0.5);
   ANA1_PREDIV = (gpioreg[PLLB_ANA1] >> 14) & 1;
   NDIV = (gpioreg[PLLB_CTRL] & 0x3ff) << ANA1_PREDIV;
   FRAC = gpioreg[PLLB_FRAC] << ANA1_PREDIV;
   int clockB = (double) (CRYSTAL * ((double)NDIV + ((double)FRAC) / ((double)(1 << 20))) + 0.5);
   ANA1_PREDIV = (gpioreg[PLLC_ANA1] >> 14) & 1;
   NDIV = (gpioreg[PLLC_CTRL] & 0x3ff) << ANA1_PREDIV;
   FRAC = gpioreg[PLLC_FRAC] << ANA1_PREDIV;
   int clockC = (double) (CRYSTAL * ((double)NDIV + ((double)FRAC) / ((double)(1 << 20))) + 0.5);
   ANA1_PREDIV = (gpioreg[PLLD_ANA1] >> 14) & 1;
   NDIV = (gpioreg[PLLD_CTRL] & 0x3ff) << ANA1_PREDIV;
   FRAC = gpioreg[PLLD_FRAC] << ANA1_PREDIV;
   int clockD = (double) (CRYSTAL * ((double)NDIV + ((double)FRAC) / ((double)(1 << 20))) + 0.5);
   sprintf(message, "             PLLA: %4d Mhz", clockA);
   osd_set(line++, 0, message);
   sprintf(message, "             PLLB: %4d Mhz", clockB);
   osd_set(line++, 0, message);
   sprintf(message, "             PLLC: %4d Mhz", clockC);
   osd_set(line++, 0, message);
   sprintf(message, "             PLLD: %4d Mhz", clockD);
   osd_set(line++, 0, message);
   sprintf(message, "        CPU Clock: %4d Mhz", get_clock_rate(ARM_CLK_ID)/1000000);
   osd_set(line++, 0, message);
   sprintf(message, "       CORE Clock: %4d Mhz", get_clock_rate(CORE_CLK_ID)/1000000);
   osd_set(line++, 0, message);
   sprintf(message, "      SDRAM Clock: %4d Mhz", get_clock_rate(SDRAM_CLK_ID)/1000000);
   osd_set(line++, 0, message);
   sprintf(message, "        Core Temp: %6.2f C", get_temp());
   osd_set(line++, 0, message);
   sprintf(message, "     Core Voltage: %6.2f V", get_voltage(COMPONENT_CORE));
   osd_set(line++, 0, message);
   sprintf(message, "  SDRAM_C Voltage: %6.2f V", get_voltage(COMPONENT_SDRAM_C));
   osd_set(line++, 0, message);
   sprintf(message, "  SDRAM_P Voltage: %6.2f V", get_voltage(COMPONENT_SDRAM_P));
   osd_set(line++, 0, message);
   sprintf(message, "  SDRAM_I Voltage: %6.2f V", get_voltage(COMPONENT_SDRAM_I));
   osd_set(line++, 0, message);
}

static void info_credits(int line) {
   osd_set(line++, 0, "Many thanks to our main developers:");
   osd_set(line++, 0, "- David Banks (hoglet)");
   osd_set(line++, 0, "- Ian Bradbury (IanB)");
   osd_set(line++, 0, "- Dominic Plunkett (dp11)");
   osd_set(line++, 0, "- Ed Spittles (BigEd)");
   osd_set(line++, 0, "");
   osd_set(line++, 0, "Thanks also to the members of stardot");
   osd_set(line++, 0, "who have provided encouragement, ideas");
   osd_set(line++, 0, "and helped with beta testing.");
}
static void info_reboot(int line) {
   reboot();
}

static void info_source_summary(int line) {
   line = show_detected_status(line);
}

static void info_cal_summary(int line) {
   if (cpld->show_cal_summary) {
      line = cpld->show_cal_summary(line);
   } else {
      sprintf(message, "show_cal_summary() not implemented");
      osd_set(line++, 0, message);
   }
}


static void info_cal_detail(int line) {
   if (cpld->show_cal_details) {
      cpld->show_cal_details(line);
   } else {
      sprintf(message, "show_cal_details() not implemented");
      osd_set(line, 0, message);
   }
}

static void info_cal_raw(int line) {
   if (cpld->show_cal_raw) {
      cpld->show_cal_raw(line);
   } else {
      sprintf(message, "show_cal_raw() not implemented");
      osd_set(line, 0, message);
   }
}

static void rebuild_menu(menu_t *menu, item_type_t type, param_t *param_ptr) {
   int i = 0;
   if (!return_at_end) {
      menu->items[i++] = (base_menu_item_t *)&back_ref;
   }
   while (param_ptr->key >= 0) {
      if (!param_ptr->hidden) {
         dynamic_item[i].type = type;
         dynamic_item[i].param = param_ptr;
         menu->items[i] = (base_menu_item_t *)&dynamic_item[i];
         i++;
      }
      param_ptr++;
   }
   if (return_at_end) {
      menu->items[i++] = (base_menu_item_t *)&back_ref;
   }
   // Add a terminator, in case the menu has had items removed
   menu->items[i++] = NULL;
}

static void rebuild_geometry_menu(menu_t *menu) {
   rebuild_menu(menu, I_GEOMETRY, geometry_get_params());
}

static void rebuild_sampling_menu(menu_t *menu) {
   rebuild_menu(menu, I_PARAM, cpld->get_params());
}

static char cpld_filenames[MAX_CPLD_FILENAMES][MAX_FILENAME_WIDTH];

static param_t cpld_filename_params[MAX_CPLD_FILENAMES];

static void rebuild_update_cpld_menu(menu_t *menu) {
   int i;
   int count;
   char cpld_dir[256];
   strncpy(cpld_dir, cpld_firmware_dir, 256);
   if (get_debug()) {
       strncat(cpld_dir, "/old", 256);
   }
   scan_cpld_filenames(cpld_filenames, cpld_dir, &count);
   for (i = 0; i < count; i++) {
      cpld_filename_params[i].key = i;
      cpld_filename_params[i].label = cpld_filenames[i];
   }
   cpld_filename_params[i].key = -1;
   rebuild_menu(menu, I_UPDATE, cpld_filename_params);
}


static void redraw_menu() {
   menu_t *menu = current_menu[depth];
   int current = current_item[depth];
   int line = 0;
   base_menu_item_t **item_ptr;
   base_menu_item_t *item;
   if (osd_state == INFO) {
      item = menu->items[current];
      // We should always be on an INFO item...
      if (item->type == I_INFO) {
         info_menu_item_t *info_item = (info_menu_item_t *)item;
         osd_set(line, ATTR_DOUBLE_SIZE, info_item->name);
         line += 2;
         info_item->show_info(line);
      }
   } else if (osd_state == MENU || osd_state == PARAM) {
      osd_set(line, ATTR_DOUBLE_SIZE, menu->name);
      line += 2;
      // Work out the longest item name
      int max = 0;
      item_ptr = menu->items;
      while ((item = *item_ptr++)) {
         int len = strlen(item_name(item));
         if (((item)->type == I_FEATURE || (item)->type == I_GEOMETRY || (item)->type == I_PARAM || (item)->type == I_UPDATE) && (len > max)){
            max = len;
         }
      }
      item_ptr = menu->items;
      int i = 0;
      while ((item = *item_ptr++)) {
         char *mp         = message;
         char sel_none    = ' ';
         char sel_open    = (i == current) ? '>' : sel_none;
         char sel_close   = (i == current) ? '<' : sel_none;
         const char *name = item_name(item);
         *mp++ = (osd_state != PARAM) ? sel_open : sel_none;
         strcpy(mp, name);
         mp += strlen(mp);
         if ((item)->type == I_FEATURE || (item)->type == I_GEOMETRY || (item)->type == I_PARAM || (item)->type == I_PARAM) {
            int len = strlen(name);
            while (len < max) {
               *mp++ = ' ';
               len++;
            }
            *mp++ = ' ';
            *mp++ = '=';
            *mp++ = (osd_state == PARAM) ? sel_open : sel_none;
            strcpy(mp, get_param_string((param_menu_item_t *)item));
            int param_len = strlen(mp);
            for (int j=0; j < param_len; j++) {
               if (*mp == '_') {
                  *mp = ' ';
               }
               mp++;
            }
         }
         *mp++ = sel_close;
         *mp++ = '\0';
         osd_set(line++, 0, message);
         i++;
      }
   }
}

static int get_key_down_duration(int key) {
   switch (key) {
   case OSD_SW1:
      return sw1counter;
   case OSD_SW2:
      return sw2counter;
   case OSD_SW3:
      return sw3counter;
   }
   return 0;
}

static void set_key_down_duration(int key, int value) {
   switch (key) {
   case OSD_SW1:
      sw1counter = value;
      break;
   case OSD_SW2:
      sw2counter = value;
      break;
   case OSD_SW3:
      sw3counter = value;
      break;
   }
}

void yuv2rgb(int maxdesat, int mindesat, int luma_scale, int black_ref, int y1_millivolts, int u1_millivolts, int v1_millivolts, int *r, int *g, int *b, int *m) {

   int desat = maxdesat;
   if (y1_millivolts >= 720) {
       desat = mindesat;
   }
   *m = 255 * (black_ref - y1_millivolts) / (black_ref - 420);
   for(int chroma_scale = 100; chroma_scale > desat; chroma_scale--) {
      int y = (luma_scale * 255 * (black_ref - y1_millivolts) / (black_ref - 420));
      int u = (chroma_scale * ((u1_millivolts - 2000) / 500) * 127);
      int v = (chroma_scale * ((v1_millivolts - 2000) / 500) * 127);

      int r1 = (((10000 * y) - ( 0001 * u) + (11398 * v)) / 1000000);
      int g1 = (((10000 * y) - ( 3946 * u) - ( 5805 * v)) / 1000000);
      int b1 = (((10000 * y) + (20320 * u) - ( 0005 * v)) / 1000000);


      *r = r1 < 1 ? 1 : r1;
      *r = r1 > 254 ? 254 : *r;
      *g = g1 < 1 ? 1 : g1;
      *g = g1 > 254 ? 254 : *g;
      *b = b1 < 1 ? 1 : b1;
      *b = b1 > 254 ? 254 : *b;

      if (*r == r1 && *g == g1 && *b == b1) {
         break;
      }
   }

   //int new_y = ((299* *r + 587* *g + 114* *b) );
   //new_y = new_y > 255000 ? 255000 : new_y;
   //if (colour == 0) {
   //    log_info("");
   //}
   //log_info("Col=%2x,  R=%4d,G=%4d,B=%4d, Y=%3d Y=%6f (%3d/256 sat)",colour,*r,*g,*b, (int) (new_y + 500)/1000, (double) new_y/1000, chroma_scale);

}


// =============================================================
// Public Methods
// =============================================================



uint32_t osd_get_equivalence(uint32_t value) {
   if (capinfo->bpp == 8) {
        return equivalence[value & 0xff] | (equivalence[(value >> 8) & 0xff] << 8) | (equivalence[(value >> 16) & 0xff] << 16) | (equivalence[value >> 24] << 24);
   } else {
        return equivalence[value & 0xf] | (equivalence[(value >> 4) & 0xf] << 4) | (equivalence[(value >> 8) & 0xf] << 8) | (equivalence[(value >> 12) & 0xf] << 12)
        | (equivalence[(value >> 16) & 0xf] << 16) | (equivalence[(value >> 20) & 0xf] << 20) | (equivalence[(value >> 24) & 0xf] << 24) | (equivalence[(value >> 28) & 0xf] << 28);
   }
}

uint32_t osd_get_palette(int index) {
   return palette_data[index];
}

void generate_palettes() {

#define bp 0x24    // b-y plus
#define bz 0x20    // b-y zero
#define bm 0x00    // b-y minus
#define rp 0x09    // r-y plus
#define rz 0x08    // r-y zero
#define rm 0x00    // r-y minus

    for(int palette = 0; palette < NUM_PALETTES; palette++) {
        for (int i = 0; i < 256; i++) {
            int r = 0;
            int g = 0;
            int b = 0;
            int m = -1;

            int luma = i & 0x12;
            int maxdesat = 99;
            int mindesat = 20;
            int luma_scale = 81;
            int black_ref = 770;

            switch (palette) {
                 case PALETTE_RGB:
                    r = (i & 1) ? 255 : 0;
                    g = (i & 2) ? 255 : 0;
                    b = (i & 4) ? 255 : 0;
                    break;

                 case PALETTE_RGBI:
                    r = (i & 1) ? 0xaa : 0x00;
                    g = (i & 2) ? 0xaa : 0x00;
                    b = (i & 4) ? 0xaa : 0x00;
                    if (i & 0x10) {                           // intensity is actually on lsb green pin on 9 way D
                       r += 0x55;
                       g += 0x55;
                       b += 0x55;
                    }
                    break;

                 case PALETTE_RGBICGA:
                    r = (i & 1) ? 0xaa : 0x00;
                    g = (i & 2) ? 0xaa : 0x00;
                    b = (i & 4) ? 0xaa : 0x00;
                    if (i & 0x10) {                           // intensity is actually on lsb green pin on 9 way D
                        r += 0x55;
                        g += 0x55;
                        b += 0x55;
                    } else {
                        if ((i & 0x07) == 3 ) {
                            g = 0x55;                          // exception for colour 6 which is brown instead of dark yellow
                        }
                    }
                    break;

                 case PALETTE_RGBISPECTRUM:
                    m = (i & 0x10) ? 0xff : 0xd7;
                    r = (i & 1) ? m : 0x00;
                    g = (i & 2) ? m : 0x00;
                    b = (i & 4) ? m : 0x00;
                    break;

                 case PALETTE_SPECTRUM:
                    switch (i & 0x09) {
                        case 0x00:
                            r = 0x00; break;
                        case 0x09:
                            r = 0xff; break;
                        default:
                            r = 0xd7; break;
                    }
                     switch (i & 0x12) {
                        case 0x00:
                            g = 0x00; break;
                        case 0x12:
                            g = 0xff; break;
                        default:
                            g = 0xd7; break;
                    }
                    switch (i & 0x24) {
                        case 0x00:
                            b = 0x00; break;
                        case 0x24:
                            b = 0xff; break;
                        default:
                            b = 0xd7; break;
                    }
                    break;

                 case PALETTE_AMSTRAD:
                    switch (i & 0x09) {
                        case 0x00:
                            r = 0x00; break;
                        case 0x09:
                            r = 0xff; break;
                        default:
                            r = 0x7f; break;
                    }
                     switch (i & 0x12) {
                        case 0x00:
                            g = 0x00; break;
                        case 0x12:
                            g = 0xff; break;
                        default:
                            g = 0x7f; break;
                    }
                    switch (i & 0x24) {
                        case 0x00:
                            b = 0x00; break;
                        case 0x24:
                            b = 0xff; break;
                        default:
                            b = 0x7f; break;
                    }
                    break;

                 case PALETTE_RrGgBb:
                    r = (i & 1) ? 0xaa : 0x00;
                    g = (i & 2) ? 0xaa : 0x00;
                    b = (i & 4) ? 0xaa : 0x00;
                    r = (i & 0x08) ? (r + 0x55) : r;
                    g = (i & 0x10) ? (g + 0x55) : g;
                    b = (i & 0x20) ? (b + 0x55) : b;
                    break;

                 case PALETTE_MDA:
                    r = (i & 0x20) ? 0xaa : 0x00;
                    r = (i & 0x10) ? (r + 0x55) : r;
                    g = r;
                    b = r;
                    break;

                 case PALETTE_ATOM_MKI: {
                    switch (i & 0x2d) {  //these five are luma independent
                        case (bz + rp):
                           yuv2rgb(maxdesat, mindesat, luma_scale, black_ref, 650, 2000, 2500, &r, &g, &b, &m); break; // red
                        case (bp + rz):
                           yuv2rgb(maxdesat, mindesat, luma_scale, black_ref, 650, 2500, 2000, &r, &g, &b, &m); break; // blue
                        case (bp + rp):
                           yuv2rgb(maxdesat, mindesat, luma_scale, black_ref, 540, 2500, 2500, &r, &g, &b, &m); break; // magenta
                        case (bz + rm):
                           yuv2rgb(maxdesat, mindesat, luma_scale, black_ref, 540, 2000, 1500, &r, &g, &b, &m); break; // cyan
                        case (bm + rz):
                           yuv2rgb(maxdesat, mindesat, luma_scale, black_ref, 420, 1500, 2000, &r, &g, &b, &m); break; // yellow
                        case (bz + rz): {
                            switch (luma) {
                                case 0x00:
                                case 0x10: //alt
                                case 0x02: //alt
                                    yuv2rgb(maxdesat, mindesat, luma_scale, black_ref, black_ref, 2000, 2000, &r, &g, &b, &m); break; // black
                                case 0x12:
                                    yuv2rgb(maxdesat, mindesat, luma_scale, black_ref, 420, 2000, 2000, &r, &g, &b, &m); break; // white (buff)
                            }
                        }
                        break;
                        case (bm + rm): {
                            switch (luma) {
                                case 0x00:
                                    yuv2rgb(maxdesat, mindesat, luma_scale, black_ref, black_ref, 2000, 2000, &r, &g, &b, &m); break; // dark green
                                case 0x10:
                                case 0x02:
                                case 0x12: //alt
                                    yuv2rgb(maxdesat, mindesat, luma_scale, black_ref, 540, 1500, 1500, &r, &g, &b, &m); break; // green
                            }
                        }
                        break;
                        case (bm + rp): {
                            switch (luma) {
                                case 0x00:
                                    yuv2rgb(maxdesat, mindesat, luma_scale, black_ref, black_ref, 2000, 2000, &r, &g, &b, &m); break; // dark orange
                                case 0x10:
                                case 0x02:
                                    yuv2rgb(maxdesat, mindesat, luma_scale, black_ref, 540, 1500, 2500, &r, &g, &b, &m); break; // normal orange
                                case 0x12:
                                    yuv2rgb(maxdesat, mindesat, luma_scale, black_ref, 420, 1500, 2500, &r, &g, &b, &m); break; // bright orange
                            }
                        }
                        break;
                    }
                 }
                 break;

                 case PALETTE_ATOM_MKI_FULL: {
                    switch (i & 0x2d) {  //these five are luma independent
                        case (bz + rp):
                           yuv2rgb(maxdesat, mindesat, luma_scale, black_ref, 650, 2000, 2500, &r, &g, &b, &m); break; // red
                        case (bp + rz):
                           yuv2rgb(maxdesat, mindesat, luma_scale, black_ref, 650, 2500, 2000, &r, &g, &b, &m); break; // blue
                        case (bp + rp):
                           yuv2rgb(maxdesat, mindesat, luma_scale, black_ref, 540, 2500, 2500, &r, &g, &b, &m); break; // magenta
                        case (bz + rm):
                           yuv2rgb(maxdesat, mindesat, luma_scale, black_ref, 540, 2000, 1500, &r, &g, &b, &m); break; // cyan
                        case (bm + rz):
                           yuv2rgb(maxdesat, mindesat, luma_scale, black_ref, 420, 1500, 2000, &r, &g, &b, &m); break; // yellow
                        case (bz + rz): {
                            switch (luma) {
                                case 0x00:
                                case 0x10: //alt
                                case 0x02: //alt
                                    yuv2rgb(maxdesat, mindesat, luma_scale, black_ref, 720, 2000, 2000, &r, &g, &b, &m); break; // black
                                case 0x12:
                                    yuv2rgb(maxdesat, mindesat, luma_scale, black_ref, 420, 2000, 2000, &r, &g, &b, &m); break; // white (buff)
                            }
                        }
                        break;
                        case (bm + rm): {
                            switch (luma) {
                                case 0x00:
                                    yuv2rgb(maxdesat, mindesat, luma_scale, black_ref, 720, 1500, 1500, &r, &g, &b, &m); break; // dark green
                                case 0x10:
                                case 0x02:
                                case 0x12: //alt
                                    yuv2rgb(maxdesat, mindesat, luma_scale, black_ref, 540, 1500, 1500, &r, &g, &b, &m); break; // green
                            }
                        }
                        break;
                        case (bm + rp): {
                            switch (luma) {
                                case 0x00:
                                    yuv2rgb(maxdesat, mindesat, luma_scale, black_ref, 720, 1500, 2500, &r, &g, &b, &m); break; // dark orange
                                case 0x10:
                                case 0x02:
                                    yuv2rgb(maxdesat, mindesat, luma_scale, black_ref, 540, 1500, 2500, &r, &g, &b, &m); break; // normal orange
                                case 0x12:
                                    yuv2rgb(maxdesat, mindesat, luma_scale, black_ref, 420, 1500, 2500, &r, &g, &b, &m); break; // bright orange
                            }
                        }
                        break;
                    }
                 }
                 break;

                 case PALETTE_ATOM_6847_EMULATORS: {
                    switch (i & 0x2d) {  //these five are luma independent
                        case (bz + rp):
                           yuv2rgb(maxdesat, mindesat, luma_scale, black_ref, 650, 2000, 2500, &r, &g, &b, &m); r = 181; g =   5; b =  34; break; // red
                        case (bp + rz):
                           yuv2rgb(maxdesat, mindesat, luma_scale, black_ref, 650, 2500, 2000, &r, &g, &b, &m); r =  34; g =  19; b = 181; break; // blue
                        case (bp + rp):
                           yuv2rgb(maxdesat, mindesat, luma_scale, black_ref, 540, 2500, 2500, &r, &g, &b, &m); r = 255; g =  28; b = 255; break; // magenta
                        case (bz + rm):
                           yuv2rgb(maxdesat, mindesat, luma_scale, black_ref, 540, 2000, 1500, &r, &g, &b, &m); r =  10; g = 212; b = 112; break; // cyan
                        case (bm + rz):
                           yuv2rgb(maxdesat, mindesat, luma_scale, black_ref, 420, 1500, 2000, &r, &g, &b, &m); r = 255; g = 255; b =  67; break; // yellow
                        case (bz + rz): {
                            switch (luma) {
                                case 0x00:
                                case 0x10: //alt
                                case 0x02: //alt
                                    yuv2rgb(maxdesat, mindesat, luma_scale, black_ref, 720, 2000, 2000, &r, &g, &b, &m); r =   9; g =   9; b =   9; break; // black
                                case 0x12:
                                    yuv2rgb(maxdesat, mindesat, luma_scale, black_ref, 420, 2000, 2000, &r, &g, &b, &m); r = 255; g = 255; b = 255; break; // white (buff)
                            }
                        }
                        break;
                        case (bm + rm): {
                            switch (luma) {
                                case 0x00:
                                    yuv2rgb(maxdesat, mindesat, luma_scale, black_ref, 720, 1500, 1500, &r, &g, &b, &m); r =   0; g =  65; b =   0; break; // dark green
                                case 0x10:
                                case 0x02:
                                case 0x12: //alt
                                    yuv2rgb(maxdesat, mindesat, luma_scale, black_ref, 540, 1500, 1500, &r, &g, &b, &m); r =  10; g = 255; b =  10; break; // green
                            }
                        }
                        break;
                        case (bm + rp): {
                            switch (luma) {
                                case 0x00:
                                    yuv2rgb(maxdesat, mindesat, luma_scale, black_ref, 720, 1500, 2500, &r, &g, &b, &m); r = 107; g =   0; b =   0; break; // dark orange
                                case 0x10:
                                case 0x02:
                                    yuv2rgb(maxdesat, mindesat, luma_scale, black_ref, 540, 1500, 2500, &r, &g, &b, &m); r = 255; g =  67; b =  10; break; // normal orange
                                case 0x12:
                                    yuv2rgb(maxdesat, mindesat, luma_scale, black_ref, 420, 1500, 2500, &r, &g, &b, &m); r = 255; g = 181; b =  67; break; // bright orange
                            }
                        }
                        break;
                    }
                 }
                 break;

                 case PALETTE_ATOM_MKII: {
                    switch (i & 0x2d) {  //these five are luma independent
                        case (bz + rp):
                           yuv2rgb(maxdesat, mindesat, luma_scale, black_ref, 650, 2000, 2500, &r, &g, &b, &m); r=0xff; g=0x00; b=0x00; break; // red
                        case (bp + rz):
                           yuv2rgb(maxdesat, mindesat, luma_scale, black_ref, 650, 2500, 2000, &r, &g, &b, &m); r=0x00; g=0x00; b=0xff; break; // blue
                        case (bp + rp):
                           yuv2rgb(maxdesat, mindesat, luma_scale, black_ref, 540, 2500, 2500, &r, &g, &b, &m); r=0xff; g=0x00; b=0xff; break; // magenta
                        case (bz + rm):
                           yuv2rgb(maxdesat, mindesat, luma_scale, black_ref, 540, 2000, 1500, &r, &g, &b, &m); r=0x00; g=0xff; b=0xff; break; // cyan
                        case (bm + rz):
                           yuv2rgb(maxdesat, mindesat, luma_scale, black_ref, 420, 1500, 2000, &r, &g, &b, &m); r=0xff; g=0xff; b=0x00; break; // yellow
                        case (bz + rz): {
                            switch (luma) {
                                case 0x00:
                                case 0x10: //alt
                                case 0x02: //alt
                                    yuv2rgb(maxdesat, mindesat, luma_scale, black_ref, black_ref, 2000, 2000, &r, &g, &b, &m); r=0x00; g=0x00; b=0x00; break; // black
                                case 0x12:
                                    yuv2rgb(maxdesat, mindesat, luma_scale, black_ref, 420, 2000, 2000, &r, &g, &b, &m); r=0xff; g=0xff; b=0xff; break; // white (buff)
                            }
                        }
                        break;
                        case (bm + rm): {
                            switch (luma) {
                                case 0x00:
                                    yuv2rgb(maxdesat, mindesat, luma_scale, black_ref, black_ref, 2000, 2000, &r, &g, &b, &m); r=0x00; g=0x00; b=0x00; break; // dark green (force black)
                                case 0x10:
                                case 0x02:
                                case 0x12: //alt
                                    yuv2rgb(maxdesat, mindesat, luma_scale, black_ref, 540, 1500, 1500, &r, &g, &b, &m); r=0x00; g=0xff; b=0x00; break; // green
                            }
                        }
                        break;
                        case (bm + rp): {
                            switch (luma) {
                                case 0x00:
                                    yuv2rgb(maxdesat, mindesat, luma_scale, black_ref, black_ref, 2000, 2000, &r, &g, &b, &m); r=0x00; g=0x00; b=0x00; break; // dark orange (force black)
                                case 0x10:
                                case 0x02:
                                    yuv2rgb(maxdesat, mindesat, luma_scale, black_ref, 540, 1500, 2500, &r, &g, &b, &m); r=0xff; g=0x00; b=0x00; break; // normal orange (force red)
                                case 0x12:
                                    yuv2rgb(maxdesat, mindesat, luma_scale, black_ref, 420, 1500, 2500, &r, &g, &b, &m); r=0xff; g=0x00; b=0x00; break; // bright orange (force red)
                            }
                        }
                        break;
                    }
                 }
                 break;

                 case PALETTE_ATOM_MKII_PLUS: {
                    switch (i & 0x2d) {  //these five are luma independent
                        case (bz + rp):
                           yuv2rgb(maxdesat, mindesat, luma_scale, black_ref, 650, 2000, 2500, &r, &g, &b, &m); r=0xff; g=0x00; b=0x00; break; // red
                        case (bp + rz):
                           yuv2rgb(maxdesat, mindesat, luma_scale, black_ref, 650, 2500, 2000, &r, &g, &b, &m); r=0x00; g=0x00; b=0xff; break; // blue
                        case (bp + rp):
                           yuv2rgb(maxdesat, mindesat, luma_scale, black_ref, 540, 2500, 2500, &r, &g, &b, &m); r=0xff; g=0x00; b=0xff; break; // magenta
                        case (bz + rm):
                           yuv2rgb(maxdesat, mindesat, luma_scale, black_ref, 540, 2000, 1500, &r, &g, &b, &m); r=0x00; g=0xff; b=0xff; break; // cyan
                        case (bm + rz):
                           yuv2rgb(maxdesat, mindesat, luma_scale, black_ref, 420, 1500, 2000, &r, &g, &b, &m); r=0xff; g=0xff; b=0x00; break; // yellow
                        case (bz + rz): {
                            switch (luma) {
                                case 0x00:
                                case 0x10: //alt
                                case 0x02: //alt
                                    yuv2rgb(maxdesat, mindesat, luma_scale, black_ref, black_ref, 2000, 2000, &r, &g, &b, &m); r=0x00; g=0x00; b=0x00; break; // black
                                case 0x12:
                                    yuv2rgb(maxdesat, mindesat, luma_scale, black_ref, 420, 2000, 2000, &r, &g, &b, &m); r=0xff; g=0xff; b=0xff; break; // white (buff)
                            }
                        }
                        break;
                        case (bm + rm): {
                            switch (luma) {
                                case 0x00:
                                    yuv2rgb(maxdesat, mindesat, luma_scale, black_ref, black_ref, 2000, 2000, &r, &g, &b, &m); r=0x00; g=0x00; b=0x00; break; // dark green (force black)
                                case 0x10:
                                case 0x02:
                                case 0x12: //alt
                                    yuv2rgb(maxdesat, mindesat, luma_scale, black_ref, 540, 1500, 1500, &r, &g, &b, &m); r=0x00; g=0xff; b=0x00; break; // green
                            }
                        }
                        break;
                        case (bm + rp): {
                            switch (luma) {
                                case 0x00:
                                    yuv2rgb(maxdesat, mindesat, luma_scale, black_ref, black_ref, 2000, 2000, &r, &g, &b, &m); r=0x00; g=0x00; b=0x00; break; // dark orange (force black)
                                case 0x10:
                                case 0x02:
                                    yuv2rgb(maxdesat, mindesat, luma_scale, black_ref, 540, 1500, 2500, &r, &g, &b, &m); break; // normal orange was r = 160; g = 80; b = 0;
                                case 0x12:
                                    yuv2rgb(maxdesat, mindesat, luma_scale, black_ref, 420, 1500, 2500, &r, &g, &b, &m); break; // bright orange was r = 255; g = 127; b = 0;
                            }
                        }
                        break;
                    }
                 }
                 break;

                 case PALETTE_ATOM_MKII_FULL: {
                    switch (i & 0x2d) {  //these five are luma independent
                        case (bz + rp):
                           yuv2rgb(maxdesat, mindesat, luma_scale, black_ref, 650, 2000, 2500, &r, &g, &b, &m); r=0xff; g=0x00; b=0x00; break; // red
                        case (bp + rz):
                           yuv2rgb(maxdesat, mindesat, luma_scale, black_ref, 650, 2500, 2000, &r, &g, &b, &m); r=0x00; g=0x00; b=0xff; break; // blue
                        case (bp + rp):
                           yuv2rgb(maxdesat, mindesat, luma_scale, black_ref, 540, 2500, 2500, &r, &g, &b, &m); r=0xff; g=0x00; b=0xff; break; // magenta
                        case (bz + rm):
                           yuv2rgb(maxdesat, mindesat, luma_scale, black_ref, 540, 2000, 1500, &r, &g, &b, &m); r=0x00; g=0xff; b=0xff; break; // cyan
                        case (bm + rz):
                           yuv2rgb(maxdesat, mindesat, luma_scale, black_ref, 420, 1500, 2000, &r, &g, &b, &m); r=0xff; g=0xff; b=0x00; break; // yellow
                        case (bz + rz): {
                            switch (luma) {
                                case 0x00:
                                case 0x10: //alt
                                case 0x02: //alt
                                    yuv2rgb(maxdesat, mindesat, luma_scale, black_ref, 720, 2000, 2000, &r, &g, &b, &m); r=0x00; g=0x00; b=0x00; break; // black
                                case 0x12:
                                    yuv2rgb(maxdesat, mindesat, luma_scale, black_ref, 420, 2000, 2000, &r, &g, &b, &m); r=0xff; g=0xff; b=0xff; break; // white (buff)
                            }
                        }
                        break;
                        case (bm + rm): {
                            switch (luma) {
                                case 0x00:
                                    yuv2rgb(maxdesat, mindesat, luma_scale, black_ref, 720, 1500, 1500, &r, &g, &b, &m); break; // dark green was r = 0; g = 31; b = 0;
                                case 0x10:
                                case 0x02:
                                case 0x12: //alt
                                    yuv2rgb(maxdesat, mindesat, luma_scale, black_ref, 540, 1500, 1500, &r, &g, &b, &m); r=0x00; g=0xff; b=0x00; break; // green
                            }
                        }
                        break;
                        case (bm + rp): {
                            switch (luma) {
                                case 0x00:
                                    yuv2rgb(maxdesat, mindesat, luma_scale, black_ref, 720, 1500, 2500, &r, &g, &b, &m); break; // dark orange was r = 31; g = 15; b = 0;
                                case 0x10:
                                case 0x02:
                                    yuv2rgb(maxdesat, mindesat, luma_scale, black_ref, 540, 1500, 2500, &r, &g, &b, &m); break; // normal orange was r = 160; g = 80; b = 0;
                                case 0x12:
                                    yuv2rgb(maxdesat, mindesat, luma_scale, black_ref, 420, 1500, 2500, &r, &g, &b, &m); break; // bright orange was r = 255; g = 127; b = 0;
                            }
                        }
                        break;
                    }
                 }
                 break;

                 case PALETTE_MONO2:
                    switch (i & 0x02) {
                        case 0x00:
                            m = 0x00; break ;
                        case 0x02:
                            m = 0xff; break ;
                    }
                    r = m; g = m; b = m;
                    break;
                 case PALETTE_MONO3:
                    switch (i & 0x12) {
                        case 0x00:
                            m = 0x00; break ;
                        case 0x10:
                        case 0x02:
                            m = 0x7f; break ;
                        case 0x12:
                            m = 0xff; break ;
                    }
                    r = m; g = m; b = m;
                    break;
                 case PALETTE_MONO4:
                    switch (i & 0x12) {
                        case 0x00:
                            m = 0x00; break ;
                        case 0x10:
                            m = 0x55; break ;
                        case 0x02:
                            m = 0xaa; break ;
                        case 0x12:
                            m = 0xff; break ;
                    }
                    r = m; g = m; b = m;
                    break;
                 case PALETTE_MONO6:
                    switch (i & 0x1b) {
                        case 0x00:
                            m = 0x00; break ;
                        case 0x08:
                            m = 0x33; break ;
                        case 0x09:
                            m = 0x66; break ;
                        case 0x19:
                            m = 0x99; break ;
                        case 0x0b:
                            m = 0xcc; break ;
                        case 0x1b:
                            m = 0xff; break ;
                    }
                    r = m; g = m; b = m;
                    break;
/*
                 case PALETTE_TI: {
                    r=g=b=0;

                    switch (i & 0x12) {   //4 luminance levels
                        case 0x00:        // if here then either black/dk blue/dk red/dk green
                        {
                            switch (i & 0x2d) {
                                case (bz+rz):
                                r = 0x00;g=0x00;b=0x00;
                                break;
                                case (bp+rz):
                                r = 0x5b;g=0x56;b=0xd7;
                                break;
                                case (bm+rp):
                                r = 0xb5;g=0x60;b=0x54;
                                break;
                                case (bm+rm):
                                r = 0x3f;g=0x9f;b=0x45;
                                break;
                            }
                        }
                        break ;
                        case 0x10:        // if here then either md green/lt blue/md red/magenta
                        {
                        switch (i & 0x2d) {
                                case (bm+rm):
                                r = 0x44;g=0xb5;b=0x4e;
                                break;
                                case (bp+rz):
                                r = 0x81;g=0x78;b=0xea;
                                break;
                                case (bm+rp):
                                r = 0xd5;g=0x68;b=0x5d;
                                break;
                                case (bp+rp):
                                r = 0xb4;g=0x69;b=0xb2;
                                break;
                            }
                        }
                        break ;
                        case 0x02:        // if here then either lt green/lt red/cyan/dk yellow
                        {
                        switch (i & 0x2d) {
                                case (bm+rm):
                                r = 0x79;g=0xce;b=0x70; //??
                                break;
                                case (bm+rp):
                                r = 0xf9;g=0x8c;b=0x81;
                                break;
                                case (bp+rm):
                                r = 0x6c;g=0xda;b=0xec;
                                break;
                                case (bm+rz):
                                r = 0xcc;g=0xc3;b=0x66;
                                break;
                            }
                        }
                        break;
                        case 0x12:        //if here then either lt yellow/gray/white (can't tell grey from white)
                        {
                        switch (i & 0x2d) {
                                case (bm+rz):
                                r = 0xde;g=0xd1;b=0x8d;
                                break;
                                case (bz+rz):
                                r = 0xff;g=0xff;b=0xff;
                                break;
                            }
                        }
                        break ;
                    }
                 }
                 break;
*/
                 case PALETTE_SPECTRUM48K:
                    r=g=b=0;

                    switch (i & 0x12) {   //3 luminance levels

                        case 0x00:        // if here then either black/BLACK blue/BLUE red/RED magenta/MAGENTA green/GREEN
                        {

                            switch (i & 0x2d) {
                                case (bz + rz):
                                r = 0x00;g=0x00;b=0x00;     //black
                                break;
                                case (bm + rz):
                                case (bm + rp): //alt
                                r = 0x00;g=0x00;b=0xd7;     //blue
                                break;
                                case (bp + rm):
                                r = 0xd7;g=0x00;b=0x00;     //red
                                break;
                                case (bz + rm):
                                case (bm + rm): //alt
                                r = 0xd7;g=0x00;b=0xd7;     //magenta
                                break;
                                case (bp + rp):
                                r = 0x00;g=0xd7;b=0x00;     //green
                                break;
                            }
                        }
                        break;
                        case 0x02:
                        case 0x10:        // if here then either magenta/MAGENTA green/GREEN cyan/CYAN yellow/YELLOW white/WHITE
                        {
                            switch (i & 0x2d) {
                                case (bz + rm):
                                case (bm + rm): //alt
                                r = 0xd7;g=0x00;b=0xd7;     //magenta
                                break;
                                case (bp + rp):
                                r = 0x00;g=0xd7;b=0x00;     //green
                                break;
                                case (bz + rp):
                                case (bm + rp): //alt
                                r = 0x00;g=0xd7;b=0xd7;     //cyan
                                break;
                                case (bp + rz):
                                case (bp + rm): //alt
                                r = 0xd7;g=0xd7;b=0x00;     //yellow
                                break;
                                case (bz + rz):
                                r = 0xd7;g=0xd7;b=0xd7;     //white
                                break;
                            }
                        }
                        break;

                        case 0x12:        //if here then YELLOW or WHITE
                        {
                        switch (i & 0x2d) {
                                case (bp + rz):
                                case (bp + rm): //alt
                                r = 0xd7;g=0xd7;b=0x00;     //yellow
                                break;
                                default:
                                r = 0xff;g=0xff;b=0xff;     //bright white
                                break;
                            }
                        }
                        break;

                    }
                    break;


                 case PALETTE_CGS24:
                    if ((i & 0x30) == 0x30) {

                    switch (i & 0x0f) {
                        case 12 :
                            r=234;g=234;b=234;
                        break;
                        case 10 :
                            r=31;g=157;b=0;
                        break;
                        case 13 :
                            r=188;g=64;b=0;
                        break;
                        case 11 :
                            r=238;g=195;b=14;
                        break;
                        case 9 :
                            r=235;g=111;b=43;
                        break;
                        case 7 :
                            r=94;g=129;b=255;
                        break;
                        case 14 :
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
                            r=235;g=111;b=43;
                        break;
                        case 7 :
                            r=47;g=83;b=255;
                        break;
                        case 14 :
                            r=124;g=255;b=234;
                        break;
                        case 1 :
                            r=152;g=32;b=255;
                        break;
                        case 6 :
                            r=188;g=223;b=255;
                        break;
                        case 15 :
                            r=94;g=94;b=94;
                        break;
                        case 8 :
                            r=234;g=255;b=39;
                        break;
                        case 4 :
                            r=138;g=103;b=255;
                        break;
                        case 3 :
                            r=140;g=140;b=140;
                        break;
                        case 2 :
                            r=31;g=196;b=140;
                        break;
                        case 5 :
                            r=199;g=78;b=255;
                        break;
                        case 0 :
                            r=255;g=255;b=255;
                        break;
                    }

                    } else {
                    r=0;g=0;b=0;
                    }
                 break;

            }
            if (m == -1) {  // calculate mono if not already set
                m = ((299 * r + 587 * g + 114 * b + 500) / 1000);
                if (m > 255) {
                   m = 255;
                }
            }
            palette_array[palette][i] = (m << 24) | (b << 16) | (g << 8) | r;
        }
        strncpy(palette_names[palette], default_palette_names[palette], MAX_NAMES_WIDTH);
    }
}

   /*
   char col[16];
   col[0] = 0b000000; // black
   col[1] = 0b000111; // light blue
   col[2] = 0b000011; // blue
   col[3] = 0b001011; // light blue
   col[4] = 0b100000; // red
   col[5] = 0b011110; // acqua;
   col[6] = 0b101010; // gray
   col[7] = 0b011111; // light cyan
   col[8] = 0b110000; // light red
   col[9] = 0b101111; // light cyan
   col[10] = 0b111011; // light dmagn
   col[11] = 0b001111; // light purple
   col[12] = 0b110100; // orange
   col[13] = 0b111110; // light yellow
   col[14] = 0b111010; // salmon
   col[15] = 0b111111; // white;


   col[0] = 0b000000; // black
   col[1] = 0b001001; // green
   col[2] = 0b010011; // blue
   col[3] = 0b001011; // light blue
   col[4] = 0b100000; // red
   col[5] = 0b101010; // gray
   col[6] = 0b110011; // dmagn
   col[7] = 0b111011; // pink
   col[8] = 0b000100; // dark green
   col[9] = 0b001100; // light green
   col[10] = 0b010101; // dark gray
   col[11] = 0b011110; // acqua
   col[12] = 0b110100; // orange
   col[13] = 0b111100; // light yellow
   col[14] = 0b111010; // salmon
   col[15] = 0b111111; // white
*/

void osd_update_palette() {
    int r = 0;
    int g = 0;
    int b = 0;
    int m = 0;
    int num_colours = (capinfo->bpp == 8) ? 256 : 16;
    int design_type = (cpld->get_version() >> VERSION_DESIGN_BIT) & 0x0F;

    //copy selected palette to current palette, translating for Atom cpld and inverted Y setting (required for 6847 direct Y connection)
    for (int i = 0; i < num_colours; i++) {
        int i_adj = i;
        if(design_type == DESIGN_ATOM) {
            switch (i) {
                case 0x00:
                    i_adj = 0x00 | (bz + rz); break;  //black
                case 0x01:
                    i_adj = 0x10 | (bz + rp); break;  //red
                case 0x02:
                    i_adj = 0x10 | (bm + rm); break;  //green
                case 0x03:
                    i_adj = 0x12 | (bm + rz); break;  //yellow
                case 0x04:
                    i_adj = 0x10 | (bp + rz); break;  //blue
                case 0x05:
                    i_adj = 0x10 | (bp + rp); break;  //magenta
                case 0x06:
                    i_adj = 0x10 | (bz + rm); break;  //cyan
                case 0x07:
                    i_adj = 0x12 | (bz + rz); break;  //white
                case 0x0b:
                    i_adj = 0x10 | (bm + rp); break;  //orange
                case 0x13:
                    i_adj = 0x12 | (bm + rp); break;  //bright orange
                case 0x08:
                    i_adj = 0x00 | (bm + rm); break;  //dark green
                case 0x10:
                    i_adj = 0x00 | (bm + rp); break;  //dark orange
                default:
                    i_adj = 0x00 | (bz + rz); break;  //black
            }
        }
        int luma = i_adj & 0x12;
        if (get_feature(F_INVERT) == INVERT_Y) {
            luma = ((~i_adj & 0x10) >> 3) | ((~i_adj & 0x02) << 3);
        }
        i_adj = (i_adj & 0xed) | luma;
        palette_data[i] = palette_array[palette][i_adj];
    }

    //scan translated palette for equivalences
    for (int i = 0; i < num_colours; i++) {
        for(int j = i; j < num_colours; j++) {
            if (palette_data[i] == palette_data[j]) {
                equivalence[i] = (char) j;
            }
        }
    }

    // modify translated palette for remaining settings
    for (int i = 0; i < num_colours; i++) {
        if (paletteFlags & BIT_MODE2_PALETTE) {
            r = customPalette[i & 0x7f] & 0xff;
            g = (customPalette[i & 0x7f]>>8) & 0xff;
            b = (customPalette[i & 0x7f]>>16) & 0xff;
            m = ((299 * r + 587 * g + 114 * b + 500) / 1000);
            if (m > 255) {
                m = 255;
            }
        } else {
            r = palette_data[i] & 0xff;
            g = (palette_data[i] >> 8) & 0xff;
            b = (palette_data[i] >>16) & 0xff;
            m = (palette_data[i] >>24);
        }
        if (get_feature(F_INVERT) == INVERT_RGB) {
            r = 255 - r;
            g = 255 - g;
            b = 255 - b;
            m = 255 - m;
        }
        if (get_feature(F_COLOUR) != COLOUR_NORMAL) {
             switch (get_feature(F_COLOUR)) {
             case COLOUR_MONO:
                r = m;
                g = m;
                b = m;
                break;
             case COLOUR_GREEN:
                r = 0;
                g = m;
                b = 0;
                break;
             case COLOUR_AMBER:
                r = m*0xdf/0xff;
                g = m;
                b = 0;
                break;
             }
        }
        if (active) {
            if (i >= (num_colours >> 1)) {
            palette_data[i] = 0xFFFFFFFF;
            } else {
            r >>= 1; g >>= 1; b >>= 1;
            palette_data[i] = 0xFF000000 | (b << 16) | (g << 8) | r;
            }
        } else {
            if ((i >= (num_colours >> 1)) && get_feature(F_SCANLINES)) {
                int scanline_intensity = get_feature(F_SCANLINESINT) ;
                r = (r * scanline_intensity)>>4;
                g = (g * scanline_intensity)>>4;
                b = (b * scanline_intensity)>>4;
                palette_data[i] = 0xFF000000 | (b << 16) | (g << 8) | r;
            } else {
                palette_data[i] = 0xFF000000 | (b << 16) | (g << 8) | r;
            }
        }
        if (get_debug()) {
            palette_data[i] |= 0x00101010;
        }
   }
   RPI_PropertyInit();
   RPI_PropertyAddTag(TAG_SET_PALETTE, num_colours, palette_data);
   RPI_PropertyProcess();
}

void osd_clear() {
   if (active) {
      memset(buffer, 0, sizeof(buffer));
      osd_update((uint32_t *) (capinfo->fb + capinfo->pitch * capinfo->height * get_current_display_buffer() + capinfo->pitch * capinfo->v_adjust + capinfo->h_adjust), capinfo->pitch);
      active = 0;
      osd_update_palette();
   }
   osd_hwm = 0;
}

void osd_clear_no_palette() {
   if (active) {
      memset(buffer, 0, sizeof(buffer));
      osd_update((uint32_t *) (capinfo->fb + capinfo->pitch * capinfo->height * get_current_display_buffer() + capinfo->pitch * capinfo->v_adjust + capinfo->h_adjust), capinfo->pitch);
      active = 0;
   }
   osd_hwm = 0;
}

int save_profile(char *path, char *name, char *buffer, char *default_buffer, char *sub_default_buffer)
{
   char *pointer = buffer;
   char param_string[80];
   param_t *param;
   int current_mode7 = geometry_get_mode();
   int i;
   int cpld_ver = (cpld->get_version() >> VERSION_DESIGN_BIT) & 0x0F;
   int index = 1;
   if (cpld_ver == DESIGN_ATOM ) {
       index = 0;
   }
   if (default_buffer != NULL) {
      if (get_feature(F_AUTOSWITCH) == AUTOSWITCH_MODE7) {

         geometry_set_mode(1);
         cpld->set_mode(1);
         pointer += sprintf(pointer, "sampling7=");
         i = index;
         param = cpld->get_params() + i;
         while(param->key >= 0) {
            pointer += sprintf(pointer, "%d,", cpld->get_value(param->key));
            i++;
            param = cpld->get_params() + i;
         }
         pointer += sprintf(pointer - 1, "\r\n") - 1;
         pointer += sprintf(pointer, "geometry7=");
         i = 1;
         param = geometry_get_params() + i;
         while(param->key >= 0) {
            pointer += sprintf(pointer, "%d,", geometry_get_value(param->key));
            i++;
            param = geometry_get_params() + i;
         }
         pointer += sprintf(pointer - 1, "\r\n") - 1;
      }

      geometry_set_mode(0);
      cpld->set_mode(0);

      pointer += sprintf(pointer, "sampling=");
      i = index;
      param = cpld->get_params() + i;
      while(param->key >= 0) {
         pointer += sprintf(pointer, "%d,", cpld->get_value(param->key));
         i++;
         param = cpld->get_params() + i;
      }
      pointer += sprintf(pointer - 1, "\r\n") - 1;
      pointer += sprintf(pointer, "geometry=");
      i = 1;
      param = geometry_get_params() + i;
      while(param->key >= 0) {
         pointer += sprintf(pointer, "%d,", geometry_get_value(param->key));
         i++;
         param = geometry_get_params() + i;
      }
      pointer += sprintf(pointer - 1, "\r\n") - 1;
      geometry_set_mode(current_mode7);
      cpld->set_mode(current_mode7);
   }

   i = 0;
   while (features[i].key >= 0) {
      if ((default_buffer != NULL && i != F_RESOLUTION && i != F_SCALING && i != F_FRONTEND && i != F_PROFILE && i != F_SUBPROFILE && (i != F_AUTOSWITCH || sub_default_buffer == NULL))
          || (default_buffer == NULL && i == F_AUTOSWITCH)) {
         strcpy(param_string, features[i].property_name);
         if (i == F_PALETTE) {
            sprintf(pointer, "%s=%s", param_string, palette_names[get_feature(i)]);
         } else {
            sprintf(pointer, "%s=%d", param_string, get_feature(i));
         }
         if (strstr(default_buffer, pointer) == NULL) {
            if (sub_default_buffer) {
               if (strstr(sub_default_buffer, pointer) == NULL) {
                  log_info("Writing sub profile entry: %s", pointer);
                  pointer += strlen(pointer);
                  pointer += sprintf(pointer, "\r\n");
               }
            } else {
               log_info("Writing profile entry: %s", pointer);
               pointer += strlen(pointer);
               pointer += sprintf(pointer, "\r\n");
            }
         }
      }
      i++;
   }
   *pointer = 0;
   return file_save(path, name, buffer, pointer - buffer);
}

void process_single_profile(char *buffer) {
   char param_string[80];
   char *prop;
   int current_mode7 = geometry_get_mode();
   int i;
   if (buffer[0] == 0) {
      return;
   }
   int cpld_ver = (cpld->get_version() >> VERSION_DESIGN_BIT) & 0x0F;
   int index = 1;
   if (cpld_ver == DESIGN_ATOM) {
       index = 0;
   }
   for (int m7 = 0; m7 < 2; m7++) {
      geometry_set_mode(m7);
      cpld->set_mode(m7);

      prop = get_prop(buffer, m7 ? "sampling7" : "sampling");
      if (prop) {
         char *prop2 = strtok(prop, ",");
         int i = index;
         while (prop2) {
            param_t *param;
            param = cpld->get_params() + i;
            if (param->key < 0) {
               log_warn("Too many sampling sub-params, ignoring the rest");
               break;
            }
            int val = atoi(prop2);
            log_debug("cpld: %s = %d", param->label, val);
            cpld->set_value(param->key, val);
            prop2 = strtok(NULL, ",");
            i++;
         }
      }

      prop = get_prop(buffer, m7 ? "geometry7" : "geometry");
      if (prop) {
         char *prop2 = strtok(prop, ",");
         int i = 1;
         while (prop2) {
            param_t *param;
            param = geometry_get_params() + i;
            if (param->key < 0) {
               log_warn("Too many sampling sub-params, ignoring the rest");
               break;
            }
            int val = atoi(prop2);
            log_debug("geometry: %s = %d", param->label, val);
            geometry_set_value(param->key, val);
            prop2 = strtok(NULL, ",");
            i++;
         }
      }

   }

   geometry_set_mode(current_mode7);
   cpld->set_mode(current_mode7);

   i = 0;
   while(features[i].key >= 0) {
      if (i != F_RESOLUTION && i != F_SCALING && i != F_FRONTEND && i != F_PROFILE && i != F_SUBPROFILE) {
         strcpy(param_string, features[i].property_name);
         prop = get_prop(buffer, param_string);
         if (prop) {
            if (i == F_PALETTE) {
                for (int j = 0; j <= features[F_PALETTE].max; j++) {
                    if (strcmp(palette_names[j], prop) == 0) {
                        set_feature(i, j);
                        break;
                    }
                }
                log_debug("profile: %s = %s",param_string, prop);
            } else {
                int val = atoi(prop);
                set_feature(i, val);
                log_debug("profile: %s = %d",param_string, val);
            }
         }
      }
      i++;
   }


   // Properties below this point are not updateable in the UI
   prop = get_prop(buffer, "keymap");
   if (prop) {
      int i = 0;
      while (*prop) {
         int val = (*prop++) - '1' + OSD_SW1;
         if (val >= OSD_SW1 && val <= OSD_SW3) {
            switch (i) {
            case 0:
               key_enter = val;
               break;
            case 1:
               key_menu_up = val;
               break;
            case 2:
               key_menu_down = val;
               break;
            case 3:
               key_value_dec = val;
               break;
            case 4:
               key_value_inc = val;
               break;
            }
         }
         i++;
      }
   }

   prop = get_prop(buffer, "actionmap");
   if (prop) {
      int i = 0;
      while (*prop && i < NUM_ACTIONS) {
         osd_state_t val = MIN_ACTION + 1 + ((*prop++) - '0');
         if (val > MIN_ACTION && val < MAX_ACTION) {
            action_map[i] = val;
         }
         i++;
      }
   }

   prop = get_prop(buffer, "cpld_firmware_dir");
   if (prop) {
      strcpy(cpld_firmware_dir, prop);
   }

   // Disable CPLDv2 specific features for CPLDv1
   if (cpld->old_firmware_support() & BIT_NORMAL_FIRMWARE_V1) {
      features[F_DEINTERLACE].max = DEINTERLACE_MA4;
      if (get_feature(F_DEINTERLACE) > features[F_DEINTERLACE].max) {
         set_feature(F_DEINTERLACE, DEINTERLACE_MA1); // TODO: Decide whether this is the right fallback
      }
   }
}

void get_autoswitch_geometry(char *buffer, int index)
{
   char *prop;
   // Default properties
   prop = get_prop(buffer, "geometry");
   if (prop) {
      char *prop2 = strtok(prop, ",");
      int i = 1;
      while (prop2) {
         param_t *param;
         param = geometry_get_params() + i;
         if (param->key < 0) {
            log_warn("Too many sampling sub-params, ignoring the rest");
            break;
         }
         int val = atoi(prop2);
         if (i == CLOCK) {
            autoswitch_info[index].clock = val;
            log_debug("autoswitch: %s = %d", param->label, val);
         }
         if (i == LINE_LEN) {
            autoswitch_info[index].line_len = val;
            log_debug("autoswitch: %s = %d", param->label, val);
         }
         if (i == CLOCK_PPM) {
            autoswitch_info[index].clock_ppm = val;
            log_debug("autoswitch: %s = %d", param->label, val);
         }
         if (i == LINES_FRAME) {
            autoswitch_info[index].lines_per_frame = val;
            log_debug("autoswitch: %s = %d", param->label, val);
         }
         if (i == SYNC_TYPE) {
            autoswitch_info[index].sync_type = val;
            log_debug("autoswitch: %s = %d", param->label, val);
         }
         prop2 = strtok(NULL, ",");
         i++;
      }
   }
   double line_time = (double) autoswitch_info[index].line_len * 1000000000 / autoswitch_info[index].clock;
   double window = (double) autoswitch_info[index].clock_ppm * line_time / 1000000;
   autoswitch_info[index].lower_limit = (int) line_time - window;
   autoswitch_info[index].upper_limit = (int) line_time + window;
   log_info("Autoswitch timings %d (%s) = %d, %d, %d, %d, %d", index, sub_profile_names[index], autoswitch_info[index].lower_limit, (int) line_time,
            autoswitch_info[index].upper_limit, autoswitch_info[index].lines_per_frame, autoswitch_info[index].sync_type);
}

void process_profile(int profile_number) {
   process_single_profile(default_buffer);
   if (has_sub_profiles[profile_number]) {
      process_single_profile(sub_default_buffer);
   } else {
      process_single_profile(main_buffer);
   }
   cycle_menus();
}

void process_sub_profile(int profile_number, int sub_profile_number) {
   if (has_sub_profiles[profile_number]) {
      int saved_autoswitch = get_feature(F_AUTOSWITCH);                   // save autoswitch so it can be disabled to manually switch sub profiles
      process_single_profile(default_buffer);
      process_single_profile(sub_default_buffer);
      set_feature(F_AUTOSWITCH, saved_autoswitch);
      process_single_profile(sub_profile_buffers[sub_profile_number]);
      cycle_menus();
   }
}

void load_profiles(int profile_number, int save_selected) {
   unsigned int bytes ;
   main_buffer[0] = 0;
   features[F_SUBPROFILE].max = 0;
   strcpy(sub_profile_names[0], NOT_FOUND_STRING);
   sub_profile_buffers[0][0] = 0;
   if (has_sub_profiles[profile_number]) {
      bytes = file_read_profile(profile_names[profile_number], DEFAULT_STRING, save_selected, sub_default_buffer, MAX_BUFFER_SIZE - 4);
      if (bytes) {
         size_t count = 0;
         scan_sub_profiles(sub_profile_names, profile_names[profile_number], &count);
         if (count) {
            features[F_SUBPROFILE].max = count - 1;
            for (int i = 0; i < count; i++) {
               file_read_profile(profile_names[profile_number], sub_profile_names[i], 0, sub_profile_buffers[i], MAX_BUFFER_SIZE - 4);
               get_autoswitch_geometry(sub_profile_buffers[i], i);
            }
         }
      }
   } else {
      features[F_SUBPROFILE].max = 0;
      strcpy(sub_profile_names[0], NONE_STRING);
      sub_profile_buffers[0][0] = 0;
      if (strcmp(profile_names[profile_number], NOT_FOUND_STRING) != 0) {
         file_read_profile(profile_names[profile_number], NULL, save_selected, main_buffer, MAX_BUFFER_SIZE - 4);
      }
   }
}

int sub_profiles_available(int profile_number) {
   return has_sub_profiles[profile_number];
}

int autoswitch_detect(int one_line_time_ns, int lines_per_frame, int sync_type) {
   if (has_sub_profiles[get_feature(F_PROFILE)]) {
      log_info("Looking for autoswitch match = %d, %d, %d", one_line_time_ns, lines_per_frame, sync_type);
      for (int i=0; i <= features[F_SUBPROFILE].max; i++) {
         //log_info("Autoswitch test: %s (%d) = %d, %d, %d, %d", sub_profile_names[i], i, autoswitch_info[i].lower_limit,
         //          autoswitch_info[i].upper_limit, autoswitch_info[i].lines_per_frame, autoswitch_info[i].sync_type );
         if (   one_line_time_ns > autoswitch_info[i].lower_limit
                && one_line_time_ns < autoswitch_info[i].upper_limit
                && lines_per_frame == autoswitch_info[i].lines_per_frame
                && sync_type == autoswitch_info[i].sync_type ) {
            log_info("Autoswitch match: %s (%d) = %d, %d, %d, %d", sub_profile_names[i], i, autoswitch_info[i].lower_limit,
                     autoswitch_info[i].upper_limit, autoswitch_info[i].lines_per_frame, autoswitch_info[i].sync_type );
            return (i);
         }
      }
   }
   return -1;
}

void osd_set(int line, int attr, char *text) {
   if (line > osd_hwm) {
       osd_hwm = line;
   }
   if (!active) {
      active = 1;
      osd_update_palette();
   }
   attributes[line] = attr;
   memset(buffer + line * LINELEN, 0, LINELEN);
   int len = strlen(text);
   if (len > LINELEN) {
      len = LINELEN;
   }
   strncpy(buffer + line * LINELEN, text, len);
   osd_update((uint32_t *) (capinfo->fb + capinfo->pitch * capinfo->height * get_current_display_buffer() + capinfo->pitch * capinfo->v_adjust + capinfo->h_adjust), capinfo->pitch);
}

int osd_active() {
   return active;
}

void osd_show_cpld_recovery_menu() {
   static char name[] = "CPLD Recovery Menu";
   update_cpld_menu.name = name;
   current_menu[0] = &main_menu;
   current_item[0] = 0;
   current_menu[1] = &info_menu;
   current_item[1] = 0;
   current_menu[2] = &update_cpld_menu;
   current_item[2] = 0;
   depth = 2;
   osd_state = MENU;
   // Change the font size to the large font (no profile will be loaded)
   set_feature(F_FONTSIZE, FONTSIZE_12X20_8);
   // Bring up the menu
   osd_refresh();
   // Add some warnings
   int line = 6;
   osd_set(line++, ATTR_DOUBLE_SIZE,  "IMPORTANT:");
   line++;
   osd_set(line++, 0, "The CPLD type (3BIT/6BIT) must match");
   osd_set(line++, 0, "the RGBtoHDMI board type you have:");
   line++;
   osd_set(line++, 0, "Use 3BIT_CPLD_vxx for Hoglet's");
   osd_set(line++, 0, "   original RGBtoHD (c) 2018 board");
   osd_set(line++, 0, "Use 6BIT_CPLD_vxx for IanB's");
   osd_set(line++, 0, "   6-bit Issue 2 (c) 2018-2019 board");
   //osd_set(line++, 0, "Use ATOM_CPLD_vxx for Hoglet's");
   //osd_set(line++, 0, "   Atom Video to HDMI (c) 2019 board");
   line++;
   osd_set(line++, 0, "Programming the wrong CPLD type may");
   osd_set(line++, 0, "cause damage to your RGBtoHDMI board.");
   osd_set(line++, 0, "Please ask for help if you are not sure.");
   line++;
   osd_set(line++, 0, "Hold 3 buttons during reset for this menu.");
}

void osd_refresh() {
   // osd_refresh is called very infrequently, for example when the mode had changed,
   // or when the OSD font size has changes. To allow menus to change depending on
   // mode, we do a full rebuild of the current menu. We also try to keep the cursor
   // on the same logic item (by matching parameter key if there is one).
   menu_t *menu = current_menu[depth];
   base_menu_item_t *item;
   if (menu && menu->rebuild) {
      // record the current item
      item = menu->items[current_item[depth]];
      // record the param associates with the current item
      int key = -1;
      if (item->type == I_FEATURE || item->type == I_GEOMETRY || item->type == I_PARAM) {
         key = ((param_menu_item_t *) item)->param->key;
      }
      // rebuild the menu
      menu->rebuild(menu);
      // try to set the cursor at the same item
      int i = 0;
      while (menu->items[i]) {
         item = menu->items[i];
         if (item->type == I_FEATURE || item->type == I_GEOMETRY || item->type == I_PARAM) {
            if (((param_menu_item_t *) item)->param->key == key) {
               current_item[depth] = i;
               // don't break here, as we need the length of the list
            }
         }
         i++;
      }
      // Make really sure we are still pointing to a valid item
      if (current_item[depth] >= i) {
         current_item[depth] = 0;
      }
   }
   if (osd_state == MENU || osd_state == PARAM || osd_state == INFO) {
      osd_clear_no_palette();
      redraw_menu();
   } else {
      osd_clear();
   }
}

int osd_key(int key) {
   item_type_t type;
   base_menu_item_t *item = current_menu[depth]->items[current_item[depth]];
   child_menu_item_t *child_item = (child_menu_item_t *)item;
   param_menu_item_t *param_item = (param_menu_item_t *)item;
   int val;
   int ret = -1;
   static int cal_count;
   static int last_vsync;
   static int last_key;
   static int first_time_calibrate = 0;
   static int first_time_restore = 0;
   static int first_time_update = 0;
   static int last_up_down_key = 0;
   switch (osd_state) {

   case IDLE:
      if (key == OSD_EXPIRED) {
         osd_clear();
         // Remain in the idle state
      } else {
         // Remember the original key pressed
         last_key = key;
         // Fire OSD_EXPIRED in 1 frames time
         ret = 1;
         // come back to DURATION
         osd_state = DURATION;
      }
      break;

   case DURATION:
      // Fire OSD_EXPIRED in 1 frames time
      ret = 1;

      // Use duration to determine action
      val = get_key_down_duration(last_key);

      // Descriminate between short and long button press as early as possible
      if (val == 0 || val > LONG_KEY_PRESS_DURATION) {
         // Calculate the logical key pressed (0..5) based on the physical key and the duration
         int key_pressed = (last_key - OSD_SW1);
         if (val) {
            // long press
            key_pressed += 3;
            // avoid key immediately auto-repeating
            set_key_down_duration(last_key, 0);
         }
         if (key_pressed < 0 || key_pressed >= NUM_ACTIONS) {
            log_warn("Key pressed (%d) out of range 0..%d ", key_pressed, NUM_ACTIONS - 1);
            osd_state = IDLE;
         } else {
            log_debug("Key pressed = %d", key_pressed);
            int action = action_map[key_pressed];
            log_debug("Action      = %d", action);
            // Transition to action state
            osd_state = action;
         }
      }
      break;

   case A0_LAUNCH:
      osd_state = MENU;
      current_menu[depth] = &main_menu;
      current_item[depth] = 0;
      if(active == 0) {
         clear_menu_bits();
      }
      redraw_menu();
      break;

   case A1_CAPTURE:
      // Capture screen shot
      osd_clear();
      capture_screenshot(capinfo, profile_names[get_feature(F_PROFILE)]);
      // Fire OSD_EXPIRED in 50 frames time
      ret = 50;
      // come back to IDLE
      osd_state = IDLE;
      break;

   case A2_CLOCK_CAL:
      // HDMI Calibration
      clear_menu_bits();
      osd_set(0, ATTR_DOUBLE_SIZE, "HDMI Calibration");
      // Record the starting value of vsync
      last_vsync = get_vsync();
      // Enable vsync
      set_vsync(1);
      // Do the actual clock calibration
      action_calibrate_clocks();
      // Initialize the counter used to limit the calibration time
      cal_count = 0;
      // Fire OSD_EXPIRED in 50 frames time
      ret = 50;
      // come back to CLOCK_CAL0
      osd_state = CLOCK_CAL0;
      break;

   case A3_AUTO_CAL:
      clear_menu_bits();
      osd_set(0, ATTR_DOUBLE_SIZE, "Auto Calibration");
      osd_set(1, 0, "Video must be static during calibration");
      action_calibrate_auto();
      // Fire OSD_EXPIRED in 50 frames time
      ret = 50;
      // come back to IDLE
      osd_state = IDLE;
      break;

   case A4_SCANLINES:
      clear_menu_bits();
      set_scanlines(1 - get_scanlines());
      if (get_scanlines()) {
         osd_set(0, ATTR_DOUBLE_SIZE, "Scanlines on");
      } else {
         osd_set(0, ATTR_DOUBLE_SIZE, "Scanlines off");
      }
      // Fire OSD_EXPIRED in 50 frames time
      ret = 50;
      // come back to IDLE
      osd_state = IDLE;
      break;

   case A5_SPARE:
   case A6_SPARE:
   case A7_SPARE:
      clear_menu_bits();
      sprintf(message, "Action %d (spare)", osd_state - (MIN_ACTION + 1));
      osd_set(0, ATTR_DOUBLE_SIZE, message);
      // Fire OSD_EXPIRED in 50 frames time
      ret = 50;
      // come back to IDLE
      osd_state = IDLE;
      break;

   case CLOCK_CAL0:
      // Fire OSD_EXPIRED in 50 frames time
      ret = 50;
      if (is_genlocked()) {
         // move on when locked
         osd_set(0, ATTR_DOUBLE_SIZE, "Genlock Succeeded");
         osd_state = CLOCK_CAL1;
      } else if (cal_count == 10) {
         // give up after 10 seconds
         osd_set(0, ATTR_DOUBLE_SIZE, "Genlock Failed");
         osd_state = CLOCK_CAL1;
         // restore the original HDMI clock
         set_vlockmode(HDMI_ORIGINAL);
      } else {
         cal_count++;
      }
      break;

   case CLOCK_CAL1:
      // Restore the original setting of vsync
      set_vsync(last_vsync);
      osd_clear();
      // back to CLOCK_IDLE
      osd_state = IDLE;
      break;

   case MENU:
      type = item->type;
      if (key == key_enter) {
         last_up_down_key = 0;
         // ENTER
         switch (type) {
         case I_MENU:
            depth++;
            current_menu[depth] = child_item->child;
            current_item[depth] = 0;
            // Rebuild dynamically populated menus, e.g. the sampling and geometry menus that are mode specific
            if (child_item->child && child_item->child->rebuild) {
               child_item->child->rebuild(child_item->child);
            }
            osd_clear_no_palette();
            redraw_menu();
            break;
         case I_FEATURE:
         case I_GEOMETRY:
         case I_PARAM:
            // Test if a toggleable param (i.e. just two legal values)
            // (this is a generalized of boolean parameters)
            if (is_toggleable_param(param_item)) {
               // If so, then just toggle it
               toggle_param(param_item);
               // Special case the return at end parameter, to keep the cursor in the same position
               if (type == I_FEATURE && param_item->param->key == F_RETURN) {
                  if (return_at_end) {
                     current_item[depth]--;
                  } else {
                     current_item[depth]++;
                  }

               }
            } else {
               // If not then move to the parameter editing state
               osd_state = PARAM;
            }
            redraw_menu();
            break;
         case I_INFO:
            osd_state = INFO;
            osd_clear_no_palette();
            redraw_menu();
            break;
         case I_BACK:
            set_setup_mode(SETUP_NORMAL);
            int cpld_ver = (cpld->get_version() >> VERSION_DESIGN_BIT) & 0x0F;
            if (cpld_ver != DESIGN_ATOM) {
                cpld->set_value(0, 0);
            }
            if (depth == 0) {
               osd_clear();
               osd_state = IDLE;
            } else {
               depth--;
               if (return_at_end == 0)
                  current_item[depth] = 0;
               osd_clear_no_palette();
               redraw_menu();
            }
            break;
         case I_SAVE: {
            int result = 0;
            int asresult = -1;
            char msg[256];
            char path[256];
            if (has_sub_profiles[get_feature(F_PROFILE)]) {
               asresult = save_profile(profile_names[get_feature(F_PROFILE)], "Default", save_buffer, NULL, NULL);
               result = save_profile(profile_names[get_feature(F_PROFILE)], sub_profile_names[get_feature(F_SUBPROFILE)], save_buffer, default_buffer, sub_default_buffer);
               sprintf(path, "%s/%s.txt", profile_names[get_feature(F_PROFILE)], sub_profile_names[get_feature(F_SUBPROFILE)]);
            } else {
               result = save_profile(NULL, profile_names[get_feature(F_PROFILE)], save_buffer, default_buffer, NULL);
               sprintf(path, "%s.txt", profile_names[get_feature(F_PROFILE)]);
            }
            if (result == 0) {
               sprintf(msg, "Saved: %s", path);
            } else {
               if (result == -1) {
                  if (asresult == 0) {
                     sprintf(msg, "Auto Switching state saved");
                  } else {
                     sprintf(msg, "Not saved (same as default)");
                  }
               } else {
                  sprintf(msg, "Error %d saving file", result);
               }

            }
            set_status_message(msg);
            // Don't re-write profile.txt here - it was
            // already written if the profile was changed
            load_profiles(get_feature(F_PROFILE), 0);
            break;
         }
         case I_RESTORE:
            if (first_time_restore == 0) {
                set_status_message("Press again to confirm restore");
                first_time_restore = 1;
            } else {
                first_time_restore = 0;
                if (has_sub_profiles[get_feature(F_PROFILE)]) {
                   file_restore(profile_names[get_feature(F_PROFILE)], "Default");
                   file_restore(profile_names[get_feature(F_PROFILE)], sub_profile_names[get_feature(F_SUBPROFILE)]);
                } else {
                   file_restore(NULL, profile_names[get_feature(F_PROFILE)]);
                }
                set_feature(F_PROFILE, get_feature(F_PROFILE));
                force_reinit();
            }
            break;
         case I_UPDATE:
            if (first_time_update == 0) {
                char msg[256];
                int major = (cpld->get_version() >> VERSION_MAJOR_BIT) & 0xF;
                int minor = (cpld->get_version() >> VERSION_MINOR_BIT) & 0xF;
                if (major == 0x0f && minor == 0x0f) {
                    sprintf(msg, "Current = BLANK: Confirm?");
                } else {
                    sprintf(msg, "Current = %s v%x.%x: Confirm?", cpld->name, major, minor);
                }
                set_status_message(msg);
                first_time_update = 1;
            } else {
                first_time_update = 0;
                // Generate the CPLD filename from the menu item
                if (get_debug()) {
                    sprintf(filename, "%s/old/%s.xsvf", cpld_firmware_dir, param_item->param->label);
                } else {
                    sprintf(filename, "%s/%s.xsvf", cpld_firmware_dir, param_item->param->label);
                }
                // Reprograme the CPLD
                update_cpld(filename);
            }
            break;
         case I_CALIBRATE:
            if (first_time_calibrate == 0) {
                set_status_message("Press again to confirm calibration");
                first_time_calibrate = 1;
            } else {
                first_time_calibrate = 0;
                osd_clear();
                osd_set(0, ATTR_DOUBLE_SIZE, "Auto Calibration");
                osd_set(1, 0, "Video must be static during calibration");
                action_calibrate_auto();
                delay_in_arm_cycles(cpu_adjust(1500000000));
                osd_clear();
                redraw_menu();
                first_time_calibrate = 0;
            }
            break;
         }
      } else if (key == key_menu_up) {

         if (first_time_calibrate != 0) {
             first_time_calibrate = 0;
             set_status_message("");
         }
         if (first_time_restore != 0) {
             first_time_restore = 0;
             set_status_message("");
         }
         if (first_time_update != 0) {
             first_time_update = 0;
             set_status_message("");
         }
         // PREVIOUS
         if (current_item[depth] == 0) {
            while (current_menu[depth]->items[current_item[depth]] != NULL)
               current_item[depth]++;
         }
         current_item[depth]--;
         if (last_up_down_key == key_menu_down && get_key_down_duration(last_up_down_key) != 0) {
            redraw_menu();
            capture_screenshot(capinfo, profile_names[get_feature(F_PROFILE)]);
            delay_in_arm_cycles(cpu_adjust(1500000000));
         }
         redraw_menu();
         last_up_down_key = key;
         //osd_state = CAPTURE;
      } else if (key == key_menu_down) {
         if (first_time_calibrate != 0) {
             first_time_calibrate = 0;
             set_status_message("");
         }
         if (first_time_restore != 0) {
             first_time_restore = 0;
             set_status_message("");
         }
         if (first_time_update != 0) {
             first_time_update = 0;
             set_status_message("");
         }
         // NEXT
         current_item[depth]++;
         if (current_menu[depth]->items[current_item[depth]] == NULL) {
            current_item[depth] = 0;
         }
         if (last_up_down_key == key_menu_up && get_key_down_duration(last_up_down_key) != 0) {
            redraw_menu();
            capture_screenshot(capinfo, profile_names[get_feature(F_PROFILE)]);
            delay_in_arm_cycles(cpu_adjust(1500000000));
         }
         redraw_menu();
         last_up_down_key = key;
      }
      break;

   case PARAM:
      type = item->type;
      if (key == key_enter) {
         // ENTER
         osd_state = MENU;
      } else {
         val = get_param(param_item);
         int delta = param_item->param->step;
         int range = param_item->param->max - param_item->param->min;
         // Get the key pressed duration, in units of ~20ms
         int duration = get_key_down_duration(key);
         // Implement an exponential function for the increment
         while (range > delta * 100 && duration > 100) {
            delta *= 10;
            duration -= 100;
         }
         if (key == key_value_dec) {
            // PREVIOUS
            val -= delta;
         } else if (key == key_value_inc) {
            // NEXT
            val += delta;
         }
         if (val < param_item->param->min) {
            val = param_item->param->max;
         }
         if (val > param_item->param->max) {
            val = param_item->param->min;
         }
         set_param(param_item, val);
      }
      redraw_menu();
      break;

   case INFO:
      if (key == key_enter) {
         // ENTER
         osd_state = MENU;
         osd_clear_no_palette();
         redraw_menu();
      } else if (key == key_menu_up) {
         if (last_up_down_key == key_menu_down && get_key_down_duration(last_up_down_key) != 0) {
            capture_screenshot(capinfo, profile_names[get_feature(F_PROFILE)]);
            delay_in_arm_cycles(cpu_adjust(1500000000));
            redraw_menu();
         }

         last_up_down_key = key;
      } else if (key == key_menu_down) {
         if (last_up_down_key == key_menu_up && get_key_down_duration(last_up_down_key) != 0) {
            capture_screenshot(capinfo, profile_names[get_feature(F_PROFILE)]);
            delay_in_arm_cycles(cpu_adjust(1500000000));
            redraw_menu();
         }
         last_up_down_key = key;
      }
      break;

   default:
      log_warn("Illegal osd state %d reached", osd_state);
      osd_state = IDLE;
   }
   return ret;
}

int get_existing_frontend(int frontend) {
    return all_frontends[frontend];
}
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
